PubInv/Ox/mech/enclosure/FreeCADAssy/ControllerSupportRT/README.md

# Files Description
These files are for a bracket to support the Controller V1 PCB to the front panel



With Controler V1 PWA (Printed Wiring Assembly).
