PubInv/Ox/docs/img/Public Invention CC0 and CC-BY-SA License Statement.pdf

Public Invention's Ox Project is an open-source hardware design for an oxygen concentrator for use by field hospitals around the world. This design concept aims to develop an oxygen concentrator that can be manufactured locally while also overcoming challenges posed by human resources, hospital location (geographically), infrastructure and logistics; in addition, this project attempts minimum documentation of their design standards necessary for local approval whilst tackling regulatory requirements for medical devices. Copyright (C) 2021 Robert Read, Ben Coombs, and Darío Hereñú.

Within this folder, all documentation files included fall under the CC0 common domain license published by the creative commons here: https://creativecommons.org/publicdomain/zero/1.0/

Likewise, all graphic art files included fall under the Attribution-ShareAlike license 4.0 International as published by the creative commons here: https://creativecommons.org/licenses/by-sa/4.0/

This program is distributed in the hope that it will be useful, but WITHOUT ANY WARRANTY; without even the implied warranty of MERCHANTABILITY or FITNESS FOR A PARTICULAR PURPOSE.
