PubInv/Ox/elec/Control Board/Control v1/resources/B24B/C545730_B24B-XADSS-N-A(LF)(SN).pdf

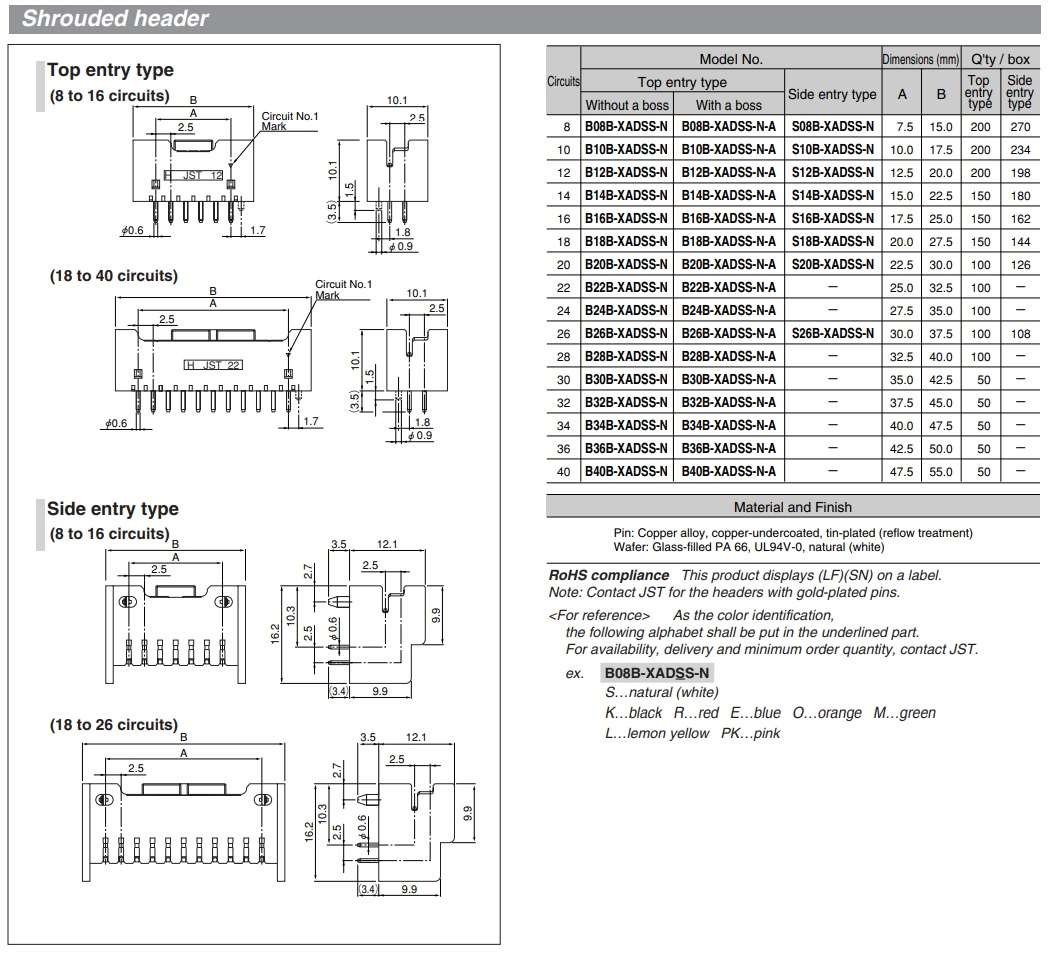
[picture p14: figure]
