PubInv/Ox/docs/img/ventmonadaptor.jpg

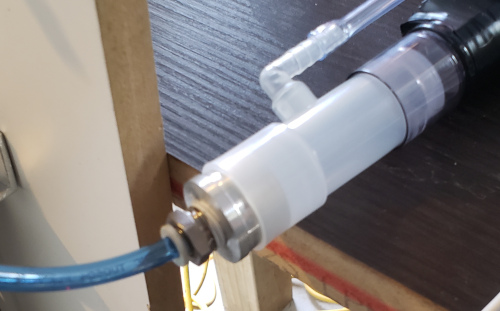
docs/img/ventmonadaptor.jpg
