PubInv/Ox/docs/OEDCS_June_2023_Version_0.1/Photos/AndersonConnectorLowVoltageHighAmperage.JPG

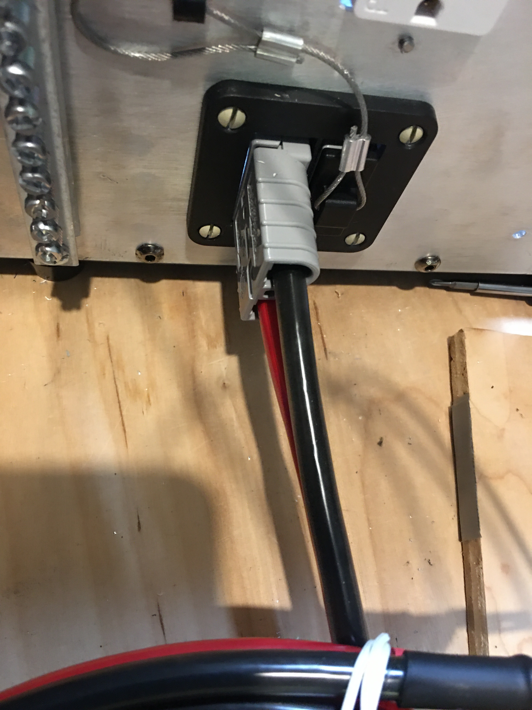
docs/OEDCS_June_2023_Version_0.1/Photos/AndersonConnectorLowVoltageHighAmperage.JPG
