PubInv/Ox/docs/OEDCS_June_2023_Version_0.1/Photos/Draft of Connected System.JPG

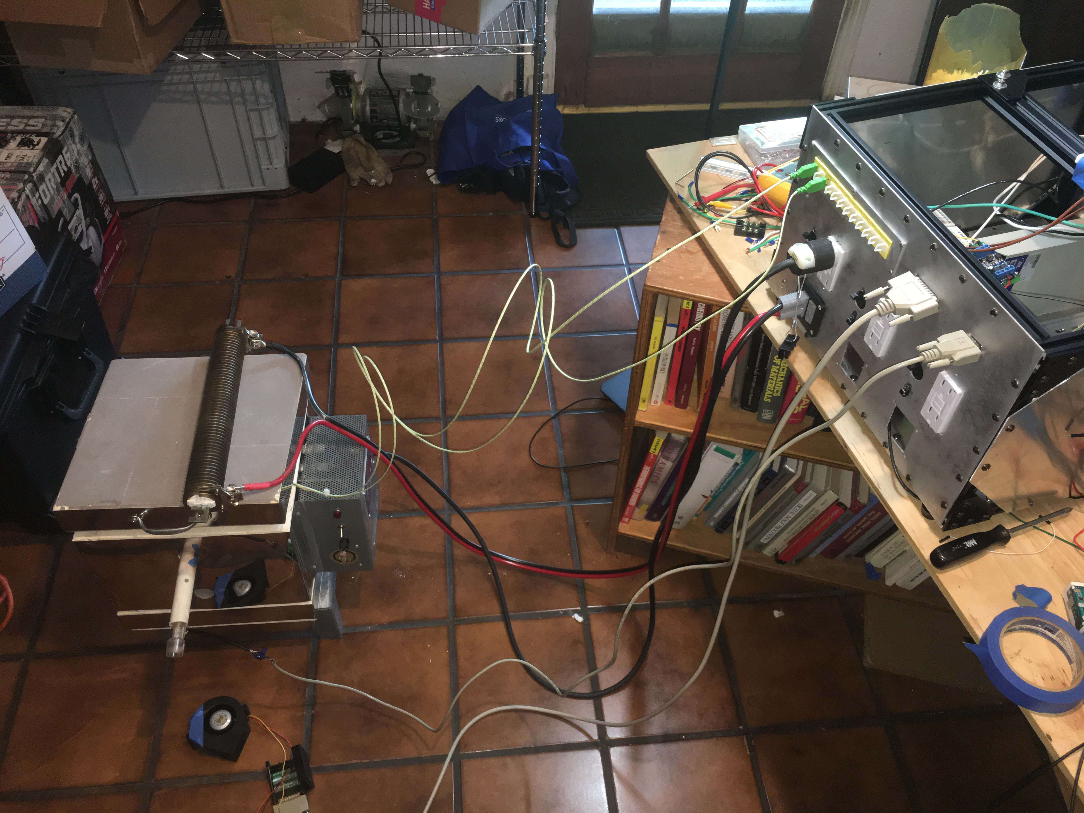
docs/OEDCS_June_2023_Version_0.1/Photos/Draft of Connected System.JPG
