PubInv/Ox/docs/OEDCS_June_2023_Version_0.1/Photos/IMG_4088.JPG

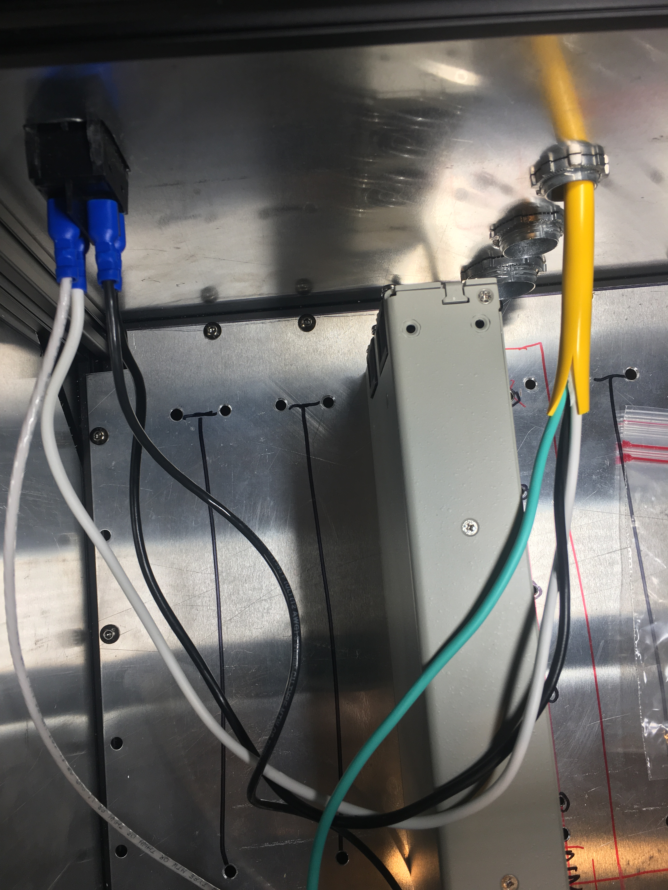
docs/OEDCS_June_2023_Version_0.1/Photos/IMG_4088.JPG
