PubInv/Ox/docs/OEDCS_June_2023_Version_0.1/Photos/OEDICOSBackOfInterFacePanel.JPG

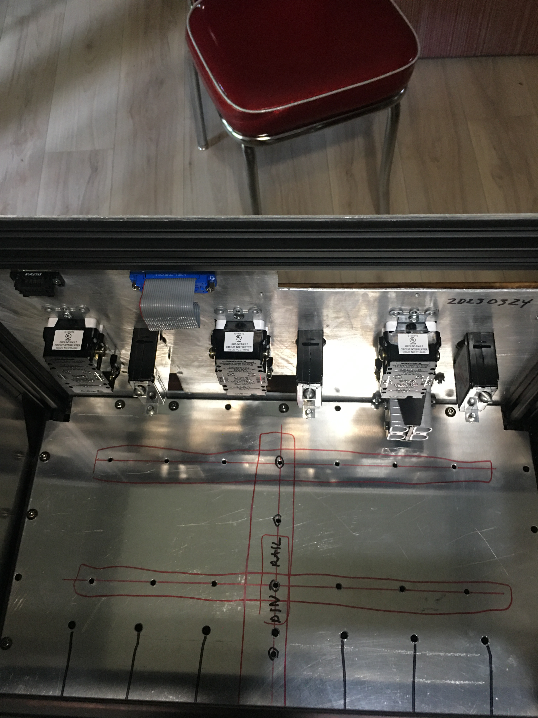
docs/OEDCS_June_2023_Version_0.1/Photos/OEDICOSBackOfInterFacePanel.JPG
