PubInv/Ox/docs/OEDCS_June_2023_Version_0.1/Photos/ThermocouplePanel(1).JPG

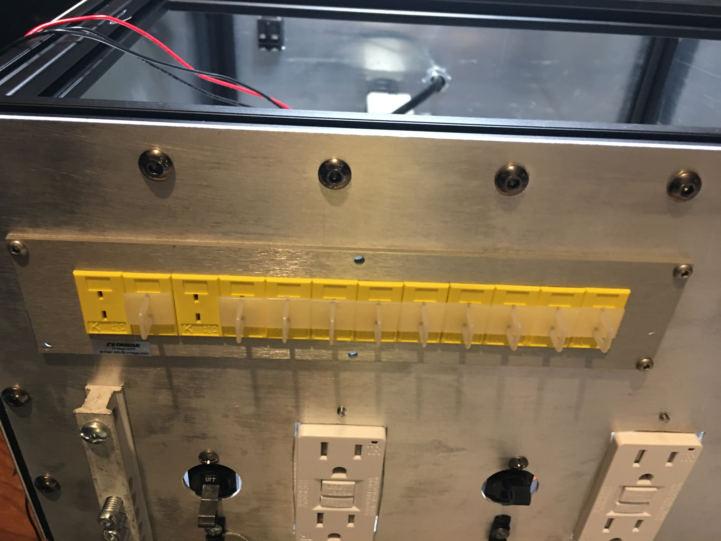
docs/OEDCS_June_2023_Version_0.1/Photos/ThermocouplePanel(1).JPG
