PubInv/Ox/docs/references/datasheets/elec/adafruit_feather_esp32.jpg

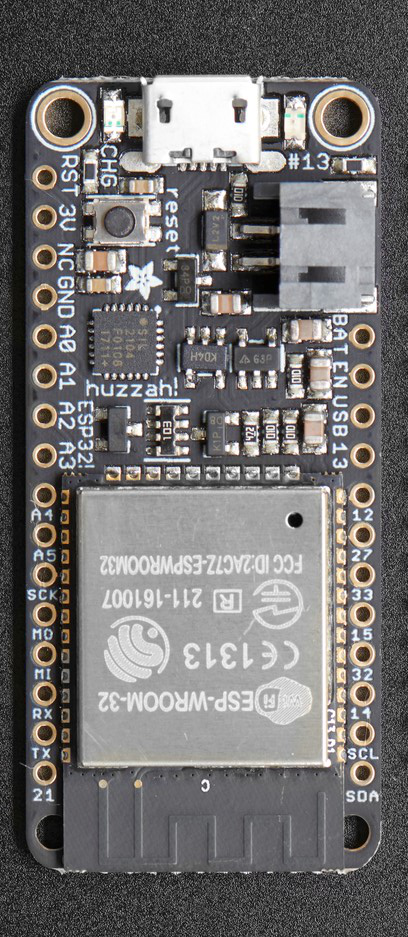
docs/references/datasheets/elec/adafruit_feather_esp32.jpg
