PubInv/Ox/docs/references/datasheets/elec/adafruit_feather_esp32_back.jpg

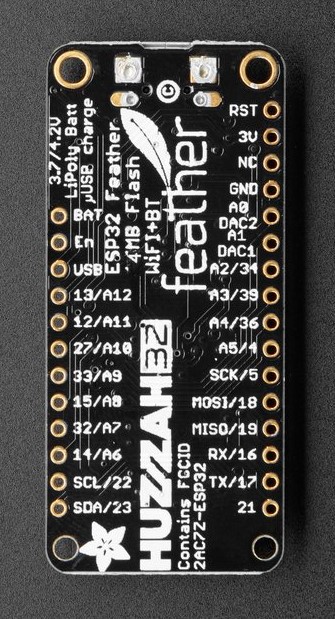
docs/references/datasheets/elec/adafruit_feather_esp32_back.jpg
