PubInv/Ox/elec/Control Board/Control v1/resources/Adafruit_MAX31850.png

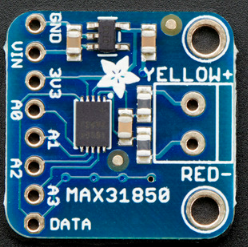
elec/Control Board/Control v1/resources/Adafruit_MAX31850.png
