PubInv/Ox/elec/Control Board/Control v1/resources/Adafruit_MAX31855.png

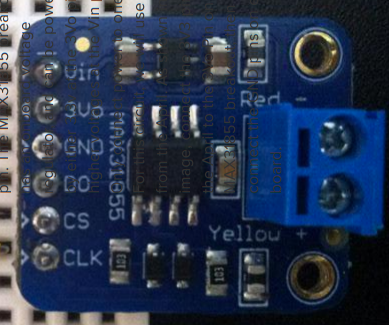
elec/Control Board/Control v1/resources/Adafruit_MAX31855.png
