PubInv/Ox/elec/Control Board/Control v1/resources/Adafruit_MAX31856.png

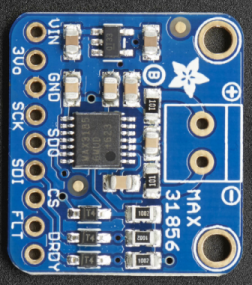
elec/Control Board/Control v1/resources/Adafruit_MAX31856.png
