PubInv/Ox/elec/Control Board/Control v1/resources/Adafruit_MCP9600.png

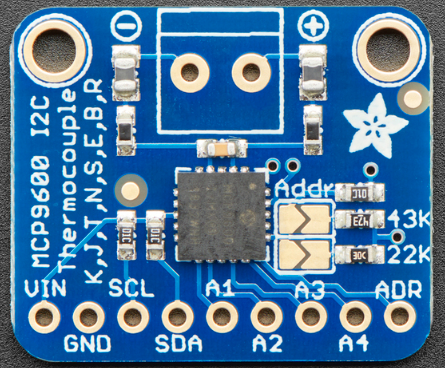
elec/Control Board/Control v1/resources/Adafruit_MCP9600.png
