PubInv/Ox/mech/enclosure/Serial_number2/Boards20230828/Due_Controller_Ethernet.jpg

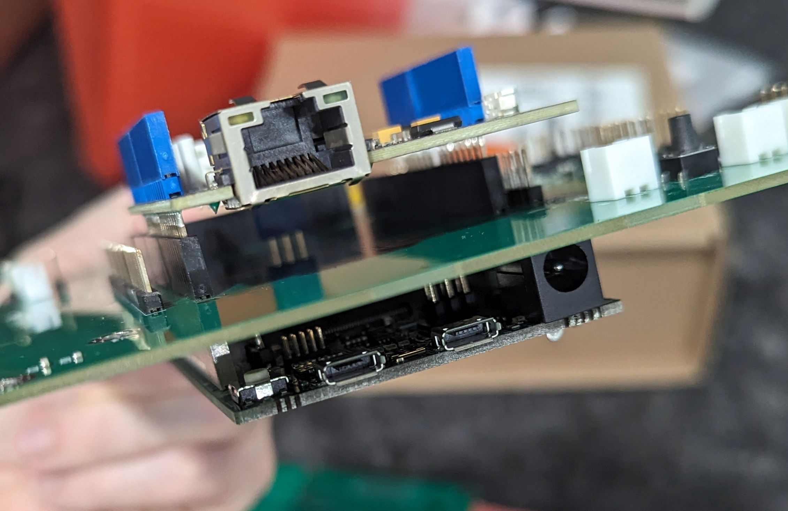
mech/enclosure/Serial_number2/Boards20230828/Due_Controller_Ethernet.jpg
