PubInv/Ox/mech/enclosure/Serial_number2/Boards20230828/ThreePCB_TwoAssy.jpg

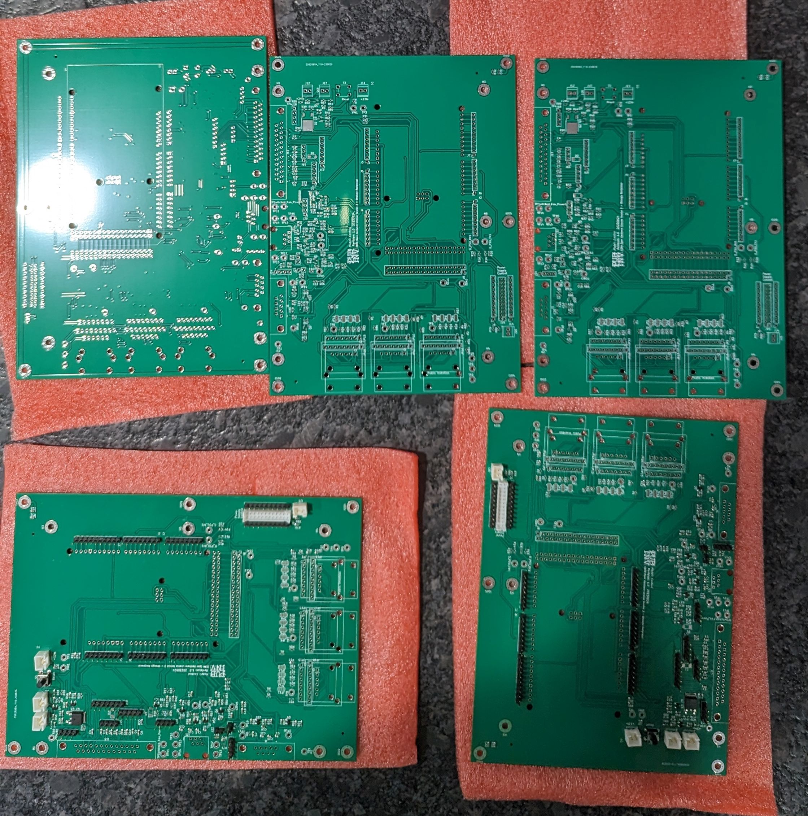
mech/enclosure/Serial_number2/Boards20230828/ThreePCB_TwoAssy.jpg
