PubInv/Ox/mech/frontpanel/Parts/Mech/mpj-j-f-thermocouple/MSS_Series.pdf

# Snap Strips

# For Mounting Miniature

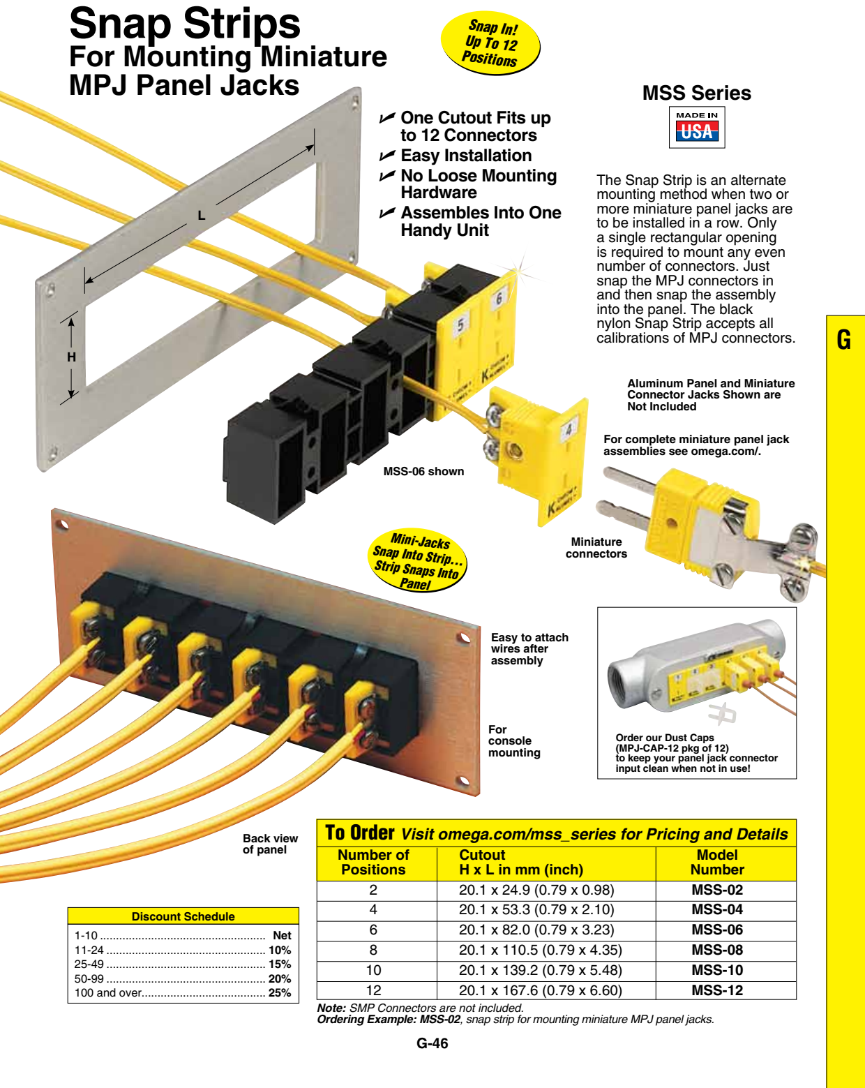
[picture p43: page 1]

# MPJ Panel Jacks

### U One Cutout Fits up to 12 Connectors U Easy Installation U No Loose Mounting Hardware U Assembles Into One Handy Unit

To Order Visit omega.com/mss_series for Pricing and Details
Number of | Cutout | Model
Positions | H x L in mm (inch) | Number
2 | 20.1 x 24.9 (0.79 x 0.98) | MSS-02
4 | 20.1 x 53.3 (0.79 x 2.10) | MSS-04
6 | 20.1 x 82.0 (0.79 x 3.23) | MSS-06
8 | 20.1 x 110.5 (0.79 x 4.35) | MSS-08
10 | 20.1 x 139.2 (0.79 x 5.48) | MSS-10
12 | 20.1 x 167.6 (0.79 x 6.60) | MSS-12

For
console
mounting

Aluminum Panel and Miniature Connector Jacks Shown are
Not Included

Easy to attach
wires after
assembly

Back view
of panel

The Snap Strip is an alternate mounting method when two or more miniature panel jacks are to be installed in a row. Only a single rectangular opening is required to mount any even number of connectors. Just snap the MPJ connectors in and then snap the assembly into the panel. The black
nylon Snap Strip accepts all calibrations of MPJ connectors.

L

H

Miniature
connectors

MSS-06 shown

For complete miniature panel jack assemblies see omega.com/.

Order our Dust Caps
(MPJ-CAP-12 pkg of 12)
to keep your panel jack connector input clean when not in use!

Note: SMP Connectors are not included.
Ordering Example: MSS-02, snap strip for mounting miniature MPJ panel jacks.
G-46

G

Mini-Jacks
Snap Into Strip...
Strip Snaps Into
Panel

Snap In!
Up To 12
Positions
1-10 | Net
11-24 | 10%
25-49 | 15%
50-99 | 20%
100 and over | 25%

Discount Schedule

## MSS Series
