PubInv/Ox/mech/frontpanel/Parts/Outlet/README.txt

This file
Found at: https://grabcad.com/library/gfci-wall-outlet-1
