PubInv/Ox/mech/frontpanel/Parts/Anderson_SB50_PanelDuplex.png

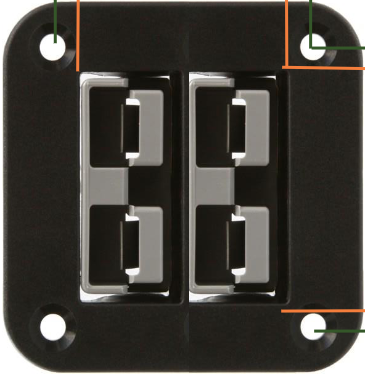
mech/frontpanel/Parts/Anderson_SB50_PanelDuplex.png
