PubInv/Ox/mech/frontpanel/Parts/DB9Female.png

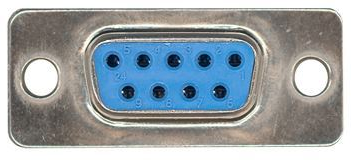
mech/frontpanel/Parts/DB9Female.png
