PubInv/Ox/mech/frontpanel/Parts/DecoratorRecepticalCover.png

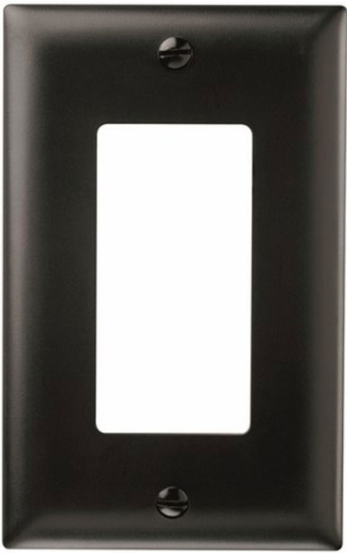
mech/frontpanel/Parts/DecoratorRecepticalCover.png
