PubInv/Ox/mech/frontpanel/Parts/Mech/DSUB9.JPG

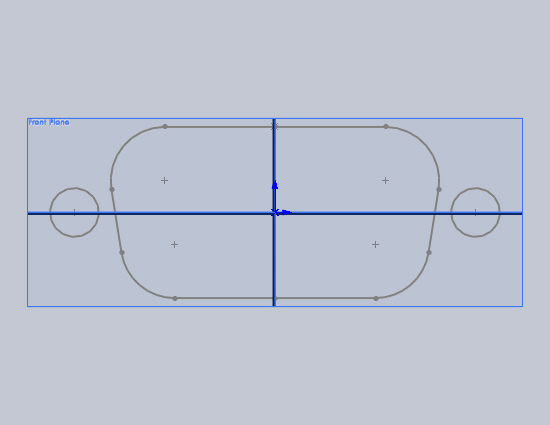
mech/frontpanel/Parts/Mech/DSUB9.JPG
