PubInv/Ox/mech/frontpanel/Parts/Mech/IEC_Receptical/IES_Cord_220_20A.jpg

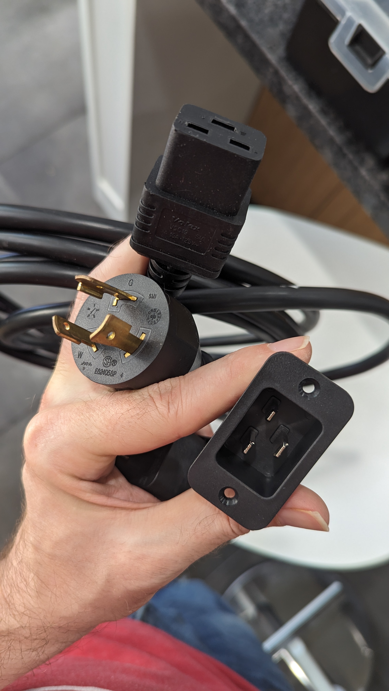
mech/frontpanel/Parts/Mech/IEC_Receptical/IES_Cord_220_20A.jpg
