PubInv/Ox/mech/frontpanel/Parts/Mech/mpj-j-f-thermocouple/example_MJP-12-K.jpg

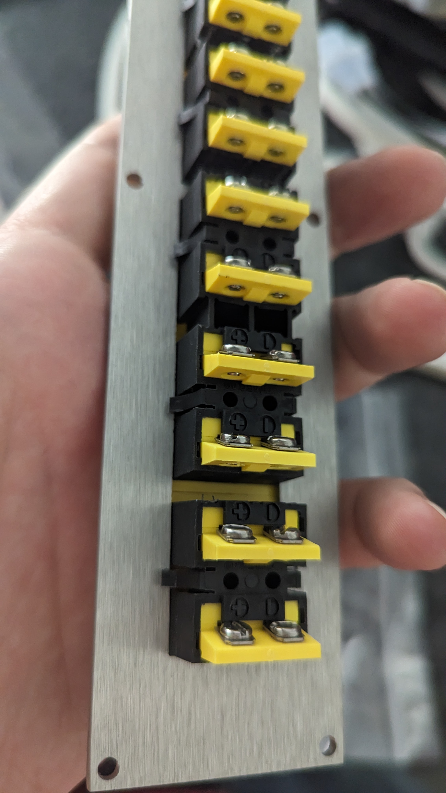
mech/frontpanel/Parts/Mech/mpj-j-f-thermocouple/example_MJP-12-K.jpg
