PubInv/Ox/mech/frontpanel/Parts/Mech/mpj-j-f-thermocouple/example_MPJ-K-F.jpg

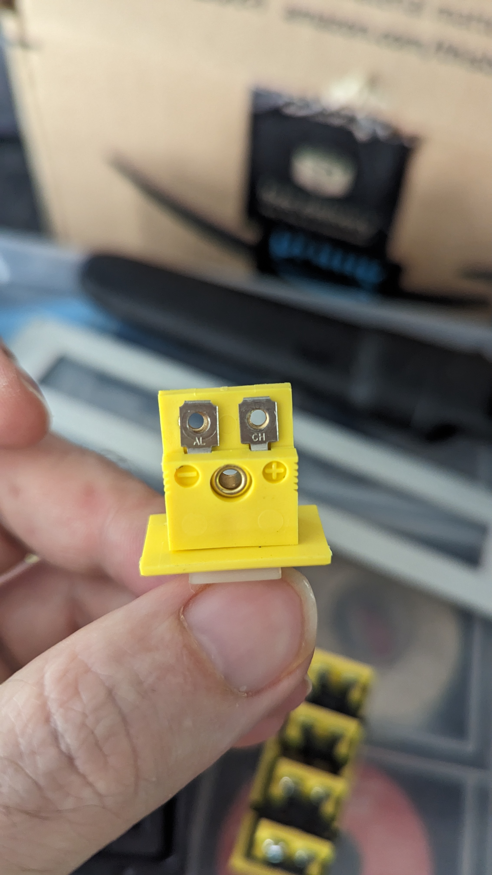
mech/frontpanel/Parts/Mech/mpj-j-f-thermocouple/example_MPJ-K-F.jpg
