PubInv/Ox/mech/frontpanel/Parts/Outlet/GFCI - Leviton Outlet.JPG

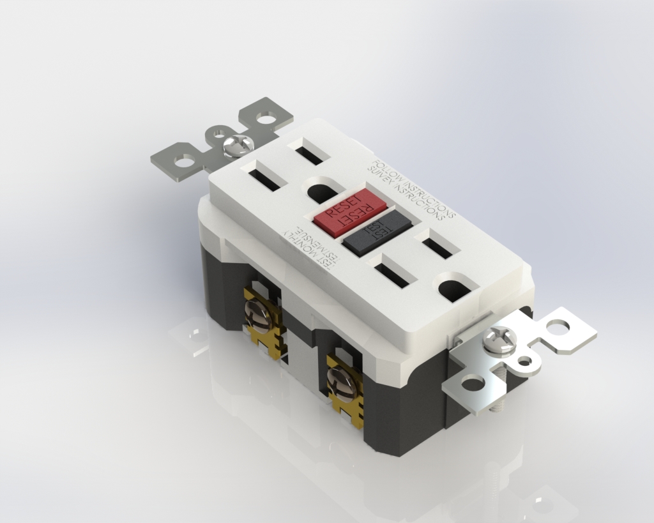
mech/frontpanel/Parts/Outlet/GFCI - Leviton Outlet.JPG
