PubInv/Ox/elec/fan_I2C/fan_I2C/parts/3D/Amphenol_54601_RT_ANGLE.step

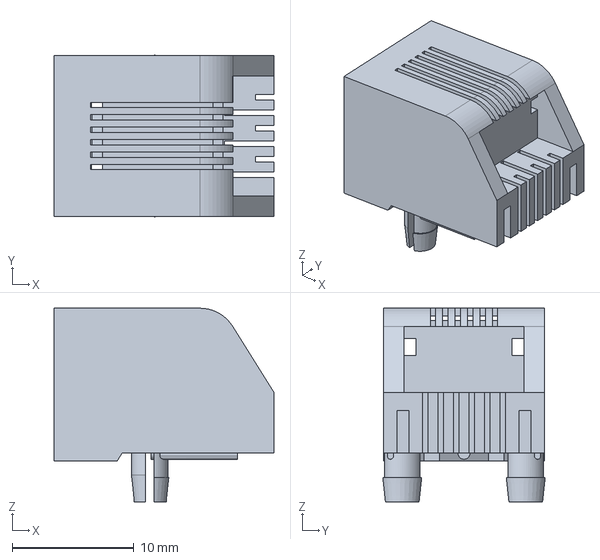
[picture p73: CAD file, 2023-09-07]
elec/fan_I2C/fan_I2C/parts/3D/Amphenol_54601_RT_ANGLE.step
18.1 x 13.4 x 15.9 mm
