PubInv/Ox/mech/enclosure/3D models/enclosure.stl

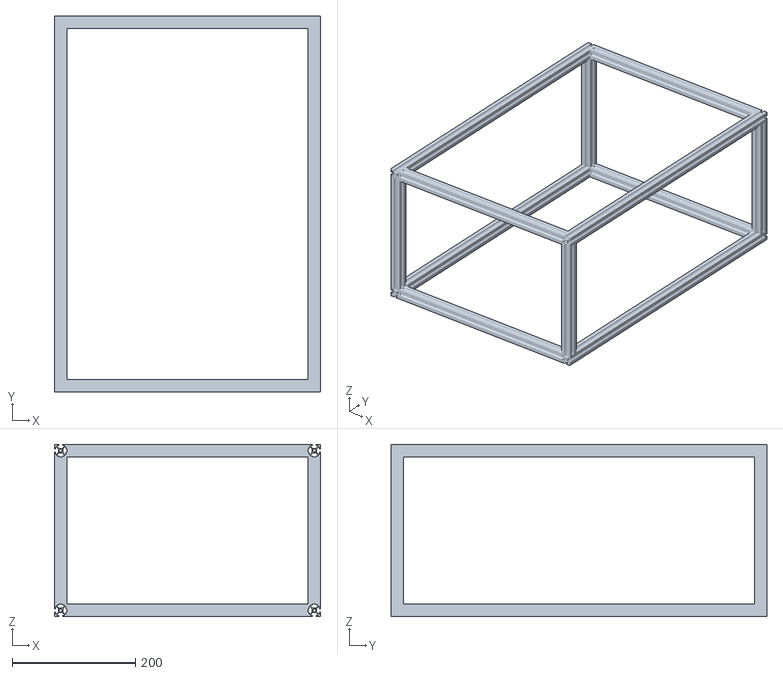
[picture p74: CAD file, 2023-09-07]
mech/enclosure/3D models/enclosure.stl
431.8 x 609.6 x 279.4
