PubInv/Ox/mech/enclosure/FreeCADAssy/ControllerSupportRT/ControllerSupportRT-PartBodySupportRT.step

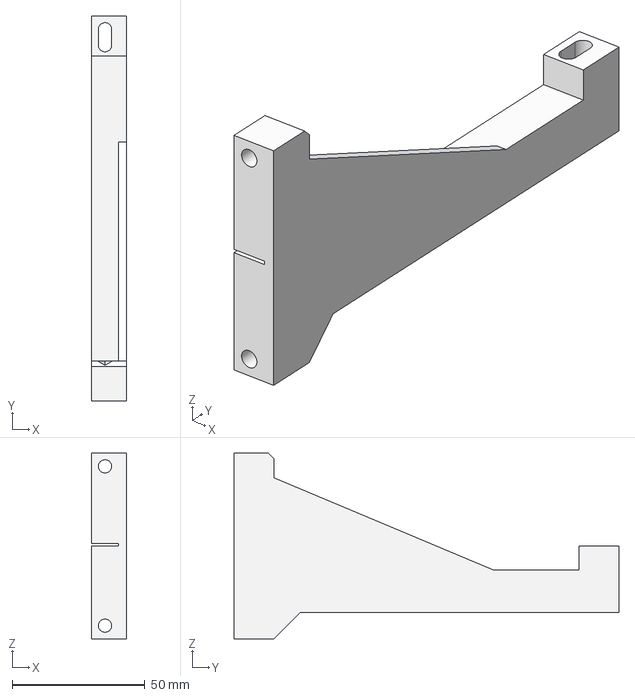
[picture p75: CAD file, 2023-09-07]
mech/enclosure/FreeCADAssy/ControllerSupportRT/ControllerSupportRT-PartBodySupportRT.step
13.0 x 145.0 x 70.0 mm
