PubInv/Ox/mech/frontpanel/Parts/Mech/Gusseted 2020 corner bracket v2.step

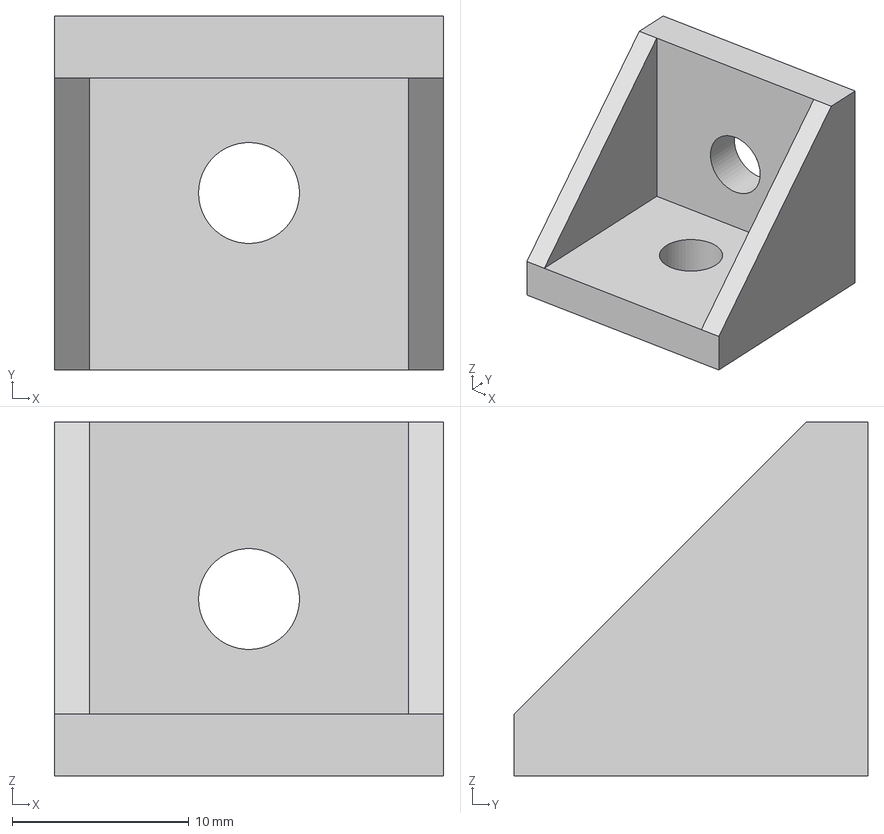
[picture p76: CAD file, 2023-09-07]
mech/frontpanel/Parts/Mech/Gusseted 2020 corner bracket v2.step
22.0 x 20.0 x 20.0 mm
