PubInv/Ox/mech/frontpanel/Parts/Mech/mpj-j-f-thermocouple/JackPanel_MJP-Part_JP6BodyJP6.step

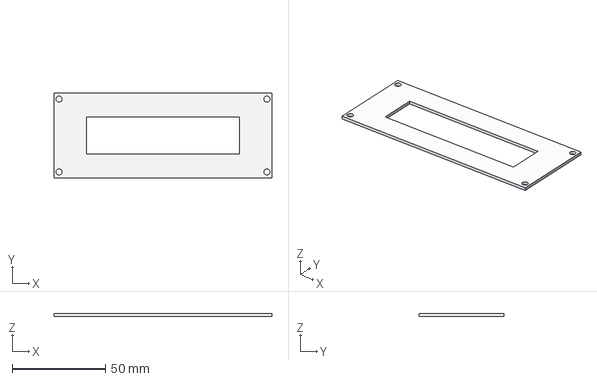
[picture p77: CAD file, 2023-09-07]
mech/frontpanel/Parts/Mech/mpj-j-f-thermocouple/JackPanel_MJP-Part_JP6BodyJP6.step
117.0 x 45.6 x 1.59 mm
