PubInv/Ox/mech/frontpanel/Parts/PowerWerx/PanelPlate_SB-PartBodySB1.step

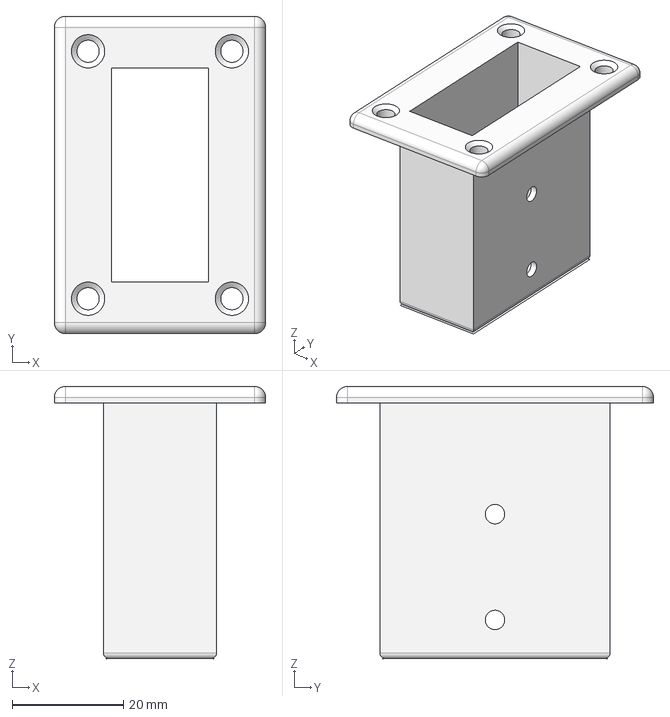
[picture p78: CAD file, 2023-09-07]
mech/frontpanel/Parts/PowerWerx/PanelPlate_SB-PartBodySB1.step
38.1 x 57.1 x 49.0 mm
