PubInv/Ox/mech/frontpanel/RearPanel3.step

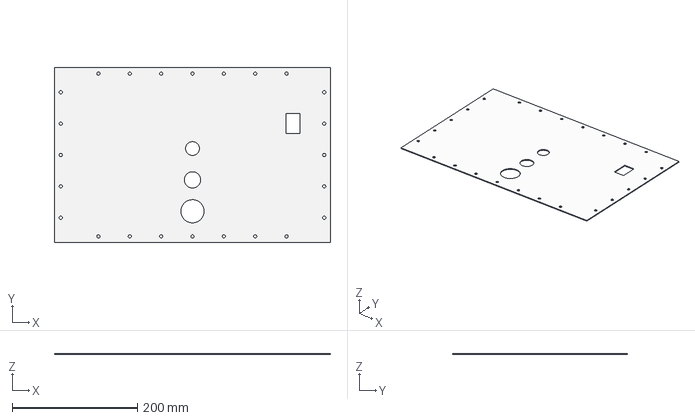
[picture p79: CAD file, 2023-09-07]
mech/frontpanel/RearPanel3.step
440.0 x 279.4 x 1.57 mm
