PubInv/Ox/mech/enclosure/FreeCADAssy/ControllerSupportRT/ControllerSupportRT-CloneBodySupportLR.step

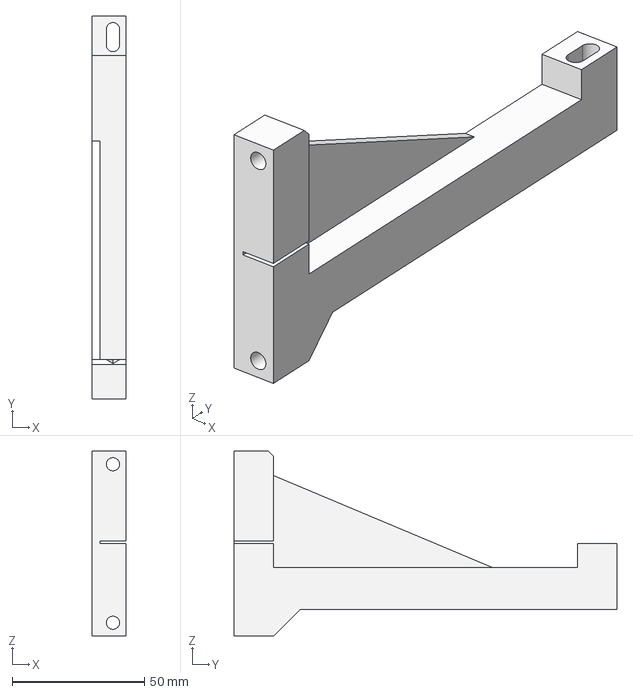
[picture p80: CAD file, 2023-09-07]
mech/enclosure/FreeCADAssy/ControllerSupportRT/ControllerSupportRT-CloneBodySupportLR.step
13.0 x 145.0 x 70.0 mm
