PubInv/Ox/mech/frontpanel/frontpanel_Rev1_3.dxf

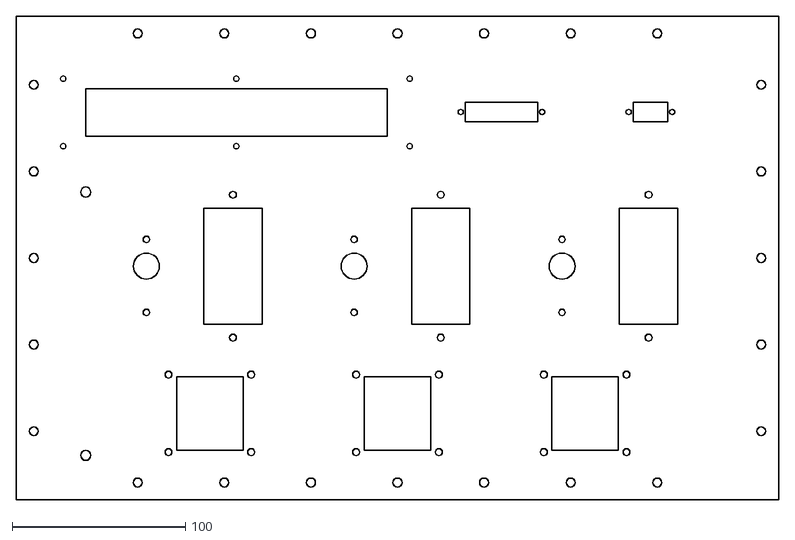
[picture p81: CAD file, 2023-09-07]
mech/frontpanel/frontpanel_Rev1_3.dxf
440.0 x 279.4
