PubInv/Ox/mech/frontpanel/Parts/Mech/alu extrusion profile 2020.step

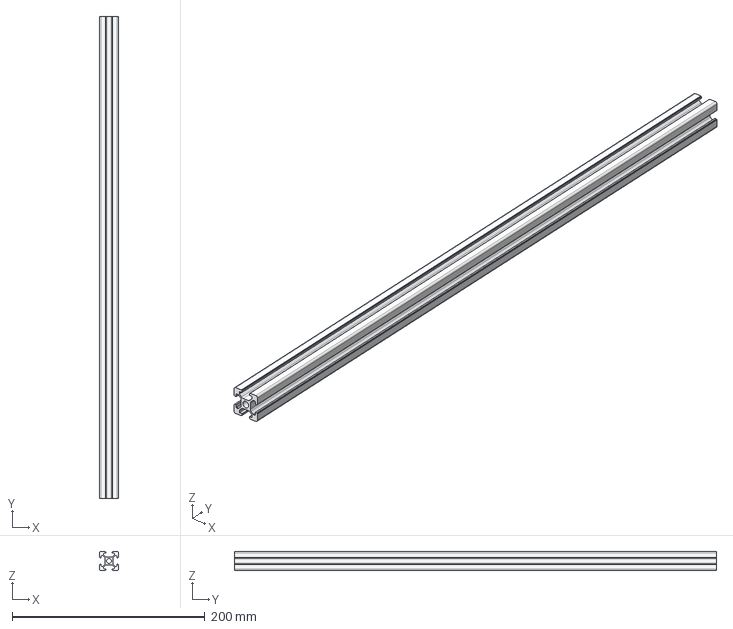
[picture p82: CAD file, 2023-09-07]
mech/frontpanel/Parts/Mech/alu extrusion profile 2020.step
20.0 x 500.0 x 20.0 mm
