PubInv/Ox/mech/frontpanel/Parts/Mech/mpj-j-f-thermocouple/MPJ-J-F Thermocouple Connector, OMEGA.STEP

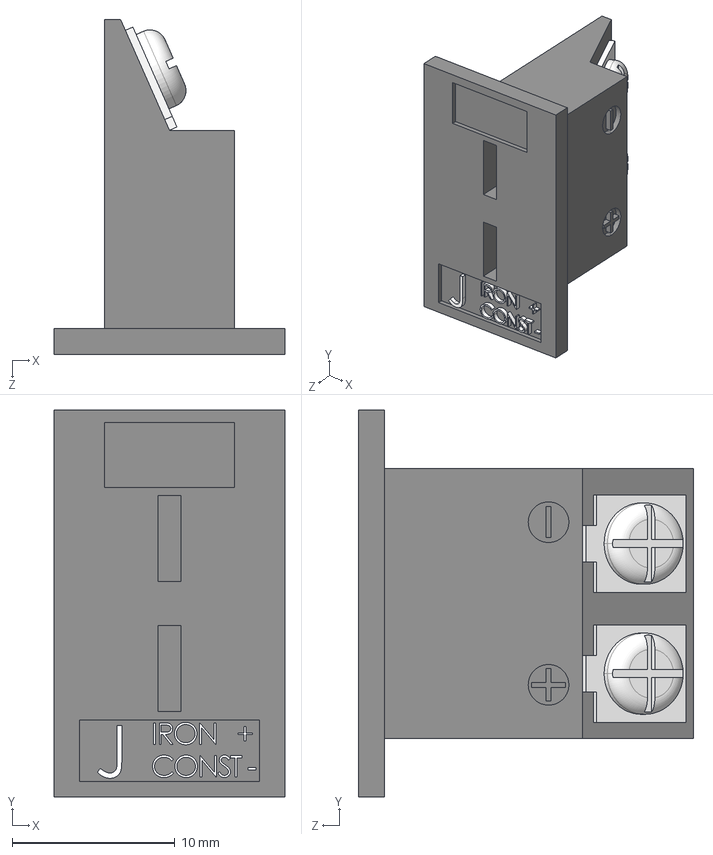
[picture p83: CAD file, 2023-09-07]
mech/frontpanel/Parts/Mech/mpj-j-f-thermocouple/MPJ-J-F Thermocouple Connector, OMEGA.STEP
14.2 x 23.8 x 20.6 mm
