PubInv/Ox/mech/frontpanel/frontpanel-PartFrontPanel2frontpanel2.step

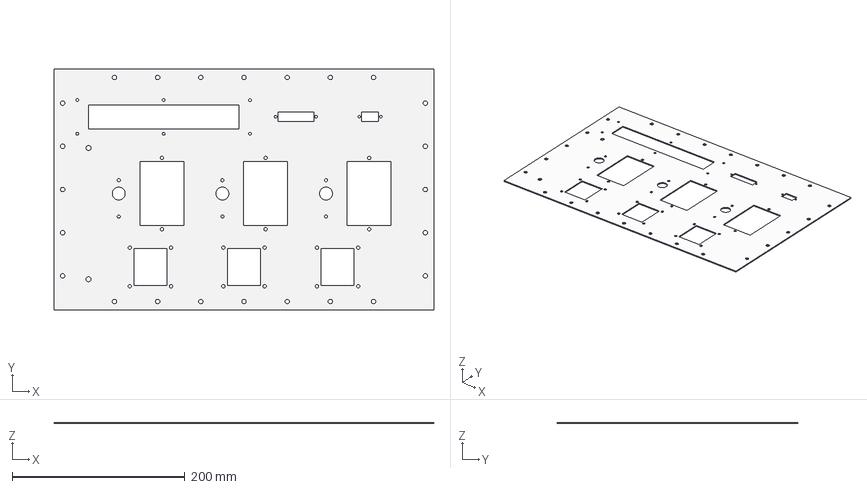
[picture p84: CAD file, 2023-09-07]
mech/frontpanel/frontpanel-PartFrontPanel2frontpanel2.step
440.0 x 279.4 x 1.57 mm
