PubInv/Ox/mech/frontpanel/Parts/Mech/Decora cover v5.step

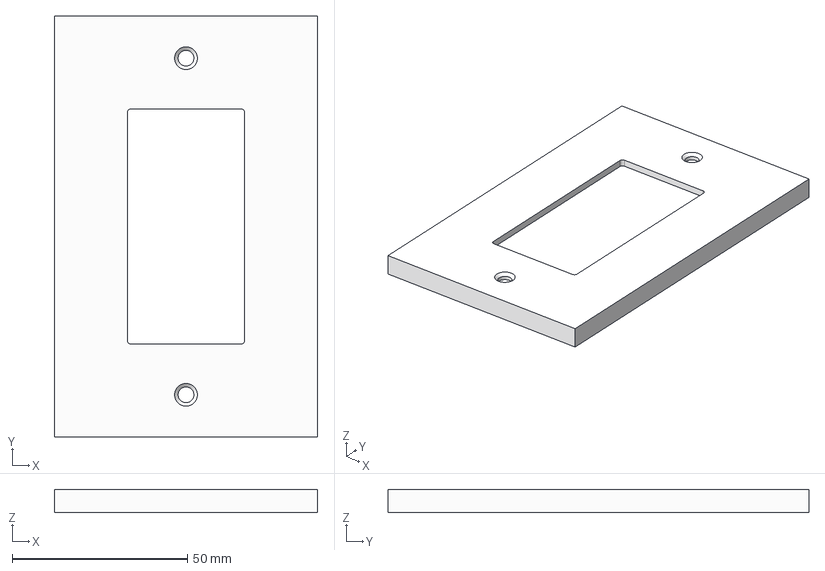
[picture p85: CAD file, 2023-09-07]
mech/frontpanel/Parts/Mech/Decora cover v5.step
75.0 x 120.0 x 6.70 mm
