PubInv/Ox/mech/frontpanel/BottomPlateV1 edit.dxf

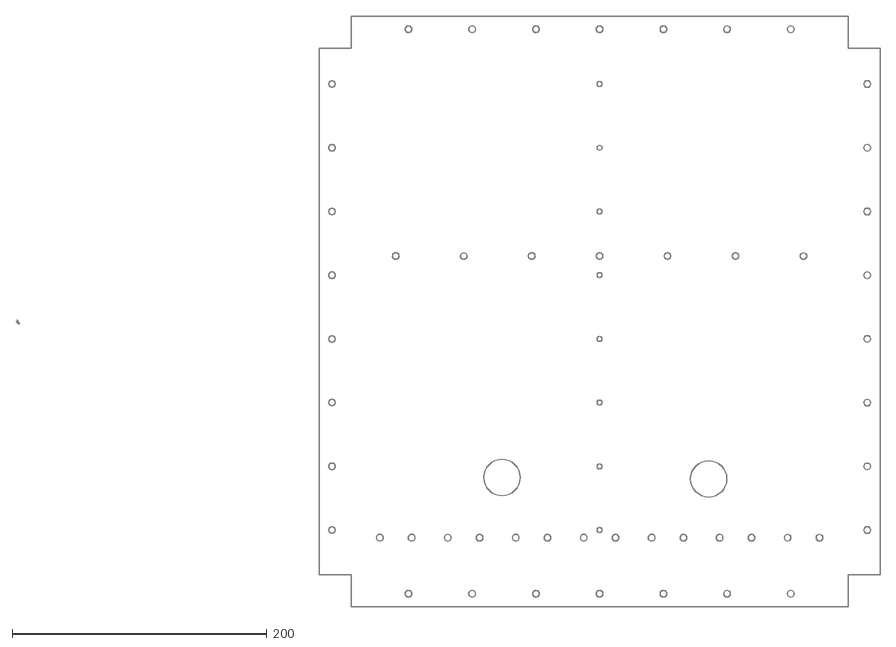
[picture p86: CAD file, 2023-09-07]
mech/frontpanel/BottomPlateV1 edit.dxf
678.0 x 463.0
