PubInv/Ox/mech/frontpanel/rear panel edit 1_3.dxf

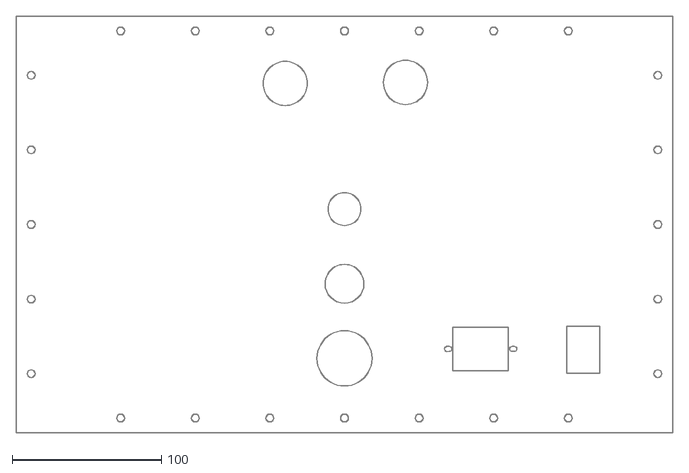
[picture p87: CAD file, 2023-09-07]
mech/frontpanel/rear panel edit 1_3.dxf
440.0 x 279.4
