PubInv/Ox/elec/Control Board/Control v1/Manufacturing Files/README.md

# Discription of these files

The files used to order Control V1 printed wiring assemblies from JLCPCB on about 20230828

* Control v1 bom and placement 28_8_2023 .zip
* Control v1Gerbers 28_8_2023.zip
* bom (3).xls
