PubInv/Ox/mech/enclosure/wiring_enclosure.png

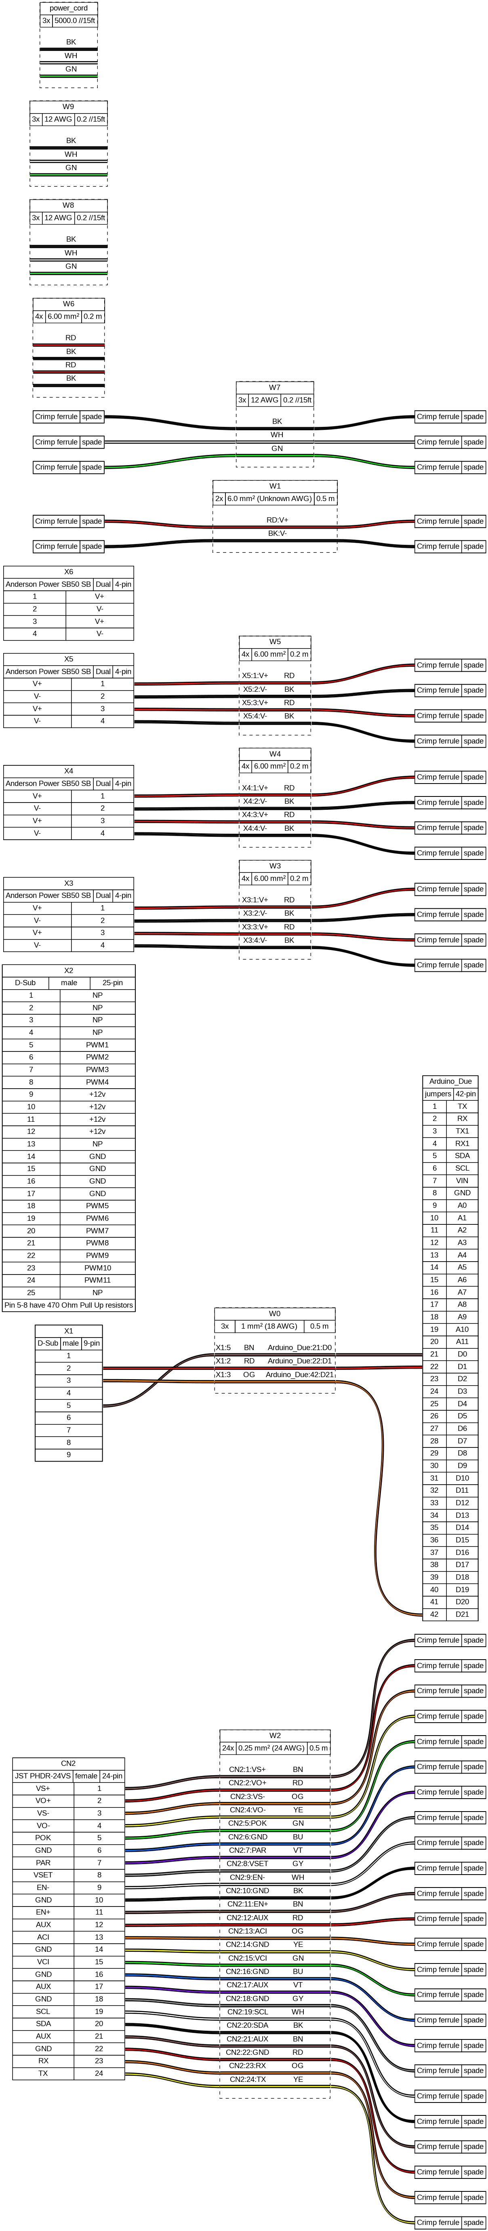
mech/enclosure/wiring_enclosure.png
