PubInv/Ox/mech/frontpanel/Parts/Mech/mpj-j-f-thermocouple/MJP1-06_Drawing.pdf

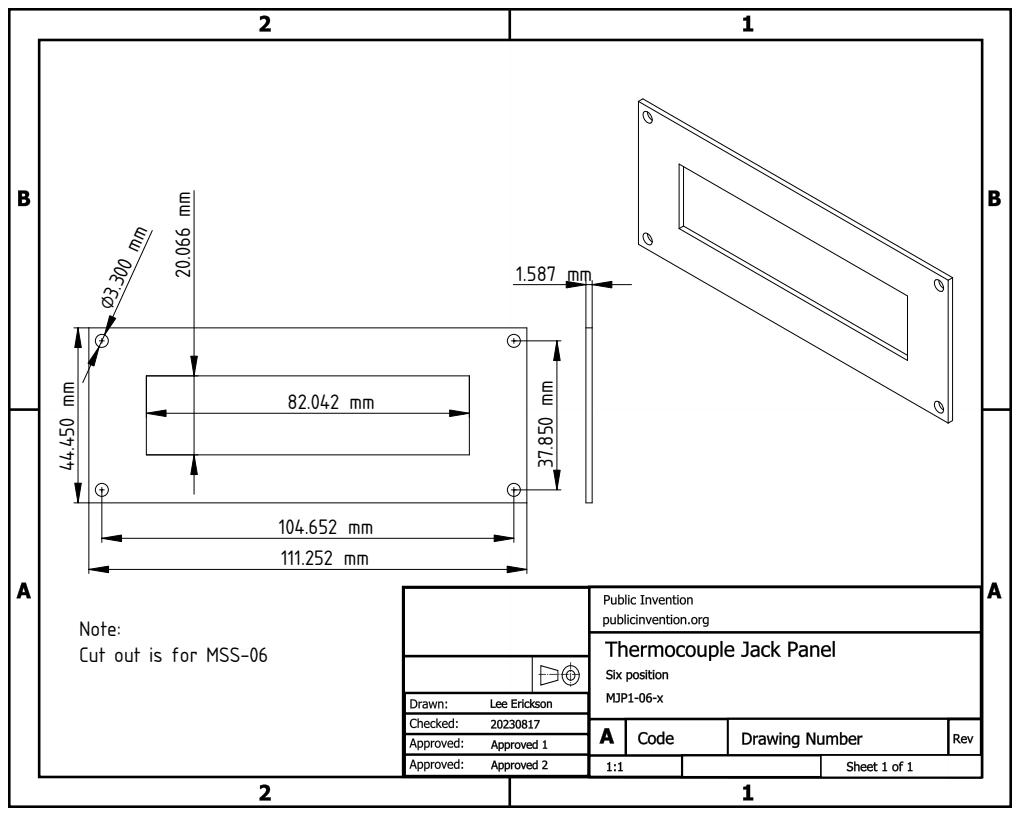
[picture p98: page 1]

Note:
Cut out is for MSS-06
