PubInv/Ox/elec/Control Board/Control v1/resources/PLUGs/C2905415_KH-2.54FH-1X4P-H8.5.pdf

# SPECIFICATIONS

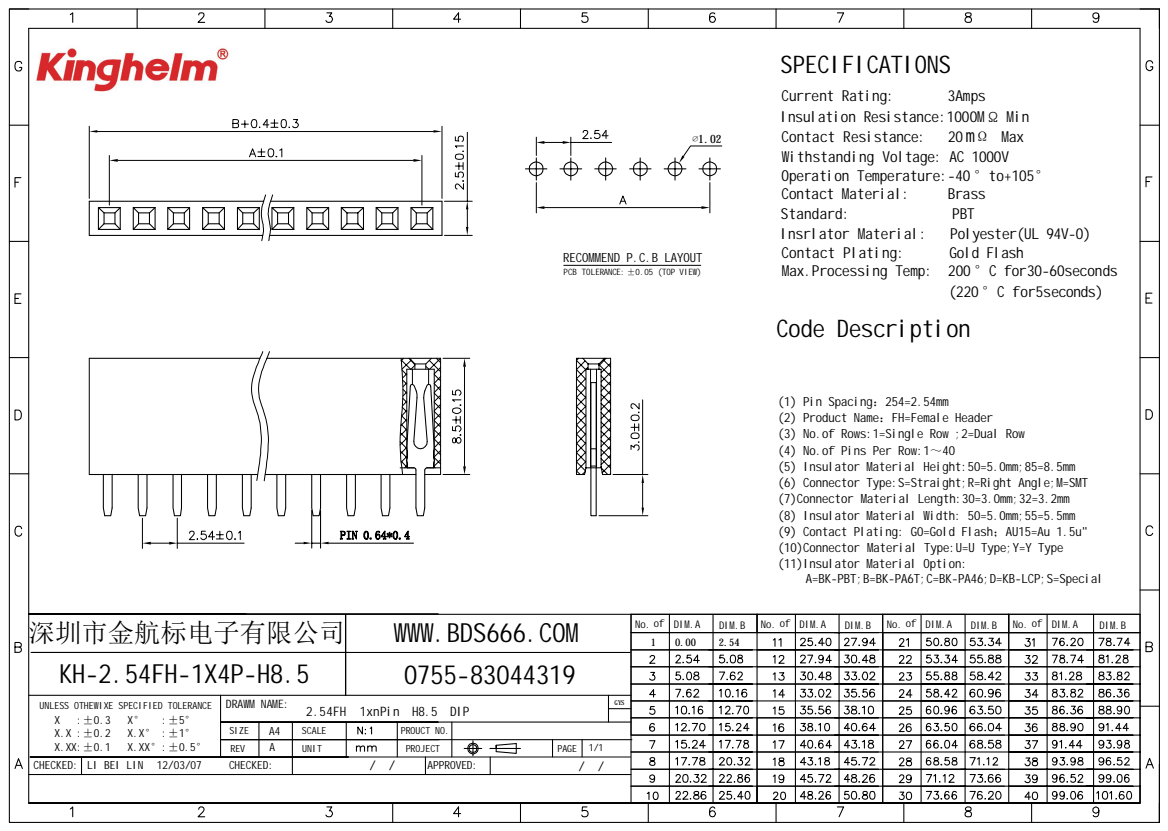
[picture p99: page 1]
2.54FH 1xnPin H8.5 DIP; CHECKED:; LI BEI LIN 12/03/07; REV; SIZE; UNIT; SCALE; UNLESS OTHEWIXE SPECIFIED TOLERANCE; DRAWM NAME:; GYS; PAGE 1/1; APPROVED:; PROUCT NO.; PROJECT; Current Rating:; 3Amps; Contact Resistance:; 20 mΩ Max; Contact Material:; Brass; Standard:; PBT; Insrlator Material:; Polyester(UL 94V-0); Contact Plating:; Gold Flash; (220 °C for5seconds) Code Description; 深圳市金航标电子有限公司; WWW.BDS666.COM

Insulation Resistance:1000M Ω Min
Withstanding Voltage: AC 1000V
Operation Temperature:-40 °to+105°
Max.Processing Temp: 200 °C for30-60seconds

RECOMMEND P.C.B LAYOUT
PCB TOLERANCE: ±0.05 (TOP VIEW)

(1) Pin Spacing：254=2.54mm
(2) Product Name：FH=Female Header
(3) No.of Rows:1=Single Row ;2=Dual Row
(4) No.of Pins Per Row:1～40
(5) Insulator Material Height:50=5.0mm;85=8.5mm
(6) Connector Type:S=Straight;R=Right Angle;M=SMT
(7)Connector Material Length:30=3.0mm;32=3.2mm
(8) Insulator Material Width: 50=5.0mm;55=5.5mm
(9) Contact Plating: G0=Gold Flash；AU15=Au 1.5u"
(10)Connector Material Type:U=U Type;Y=Y Type
(11)Insulator Material Option:
A=BK-PBT;B=BK-PA6T;C=BK-PA46;D=KB-LCP;S=Special

No. of | DIM.A DIM.B | No. of | DIM.A | DIM.B No. of | DIM.A DIM.B | No. of | DIM.A | DIM.B
1 | 0.00 | 2.54
