PubInv/Ox/mech/frontpanel/Parts/PowerWerx/PanelPlate_SB1.pdf

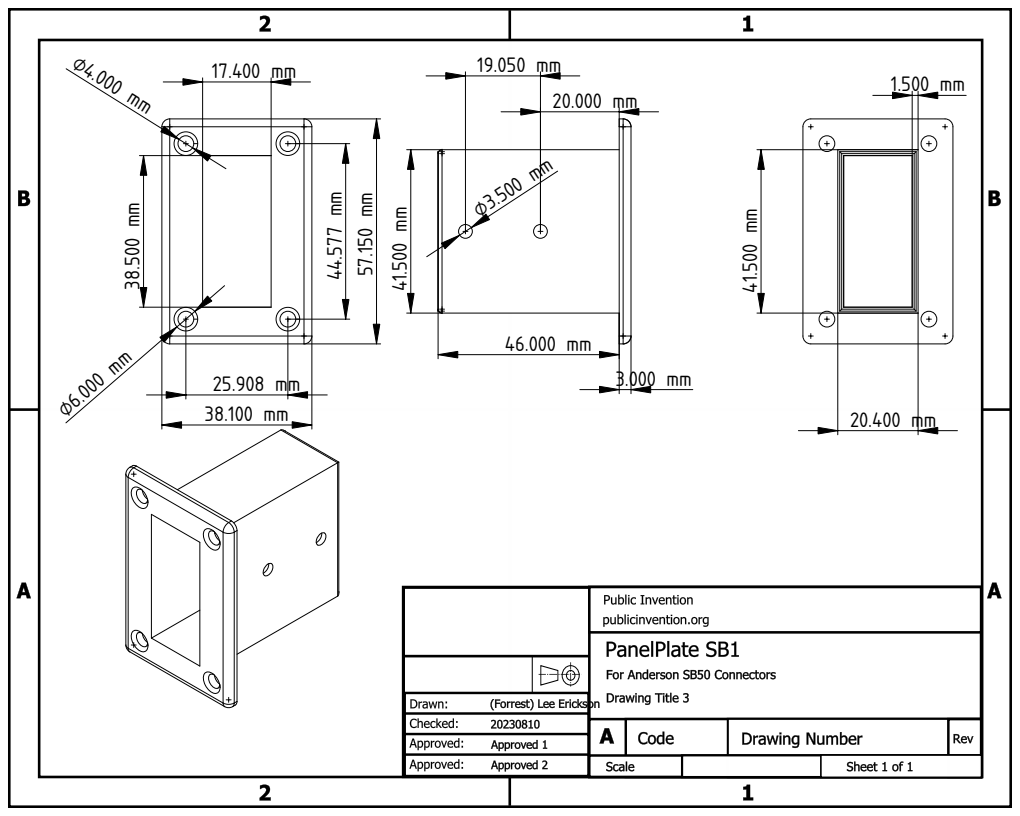
[picture p117: page 1]
