PubInv/Ox/mech/frontpanel/Parts/PowerWerx/PanelPlate_SB2.pdf

m 1.500

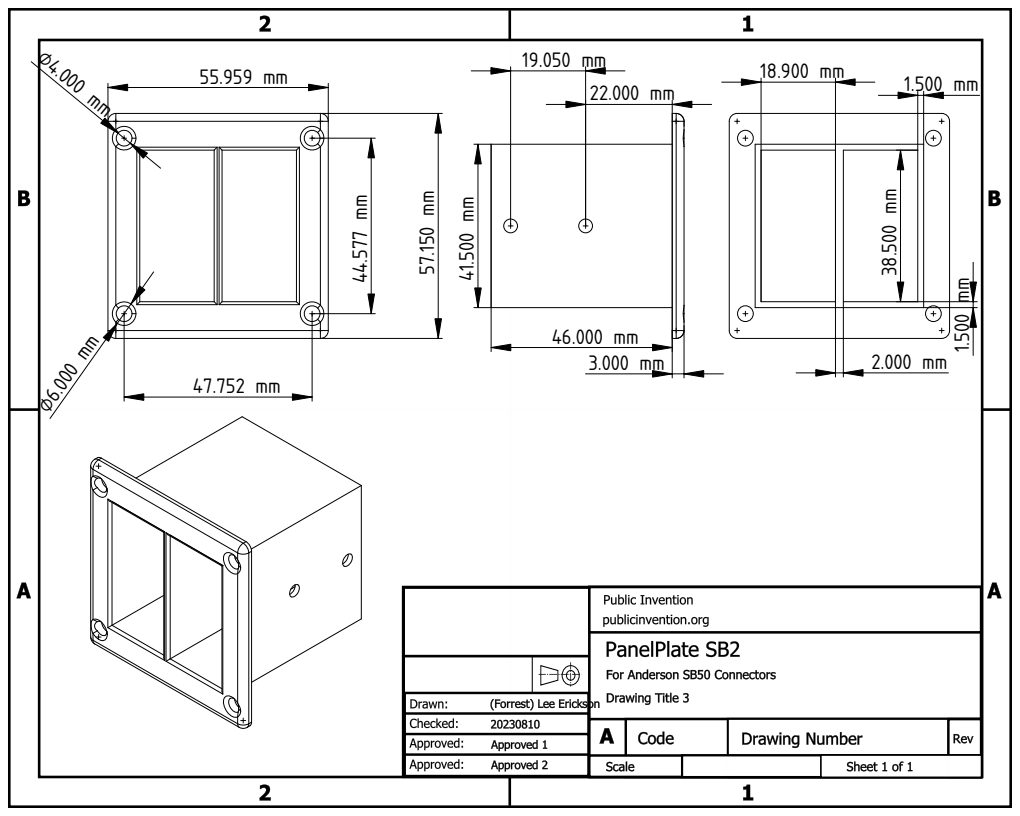
[picture p118: page 1]
