PubInv/Ox/mech/frontpanel/Parts/Mech/mpj-j-f-thermocouple/MSS_B0282761 REV-A.pdf

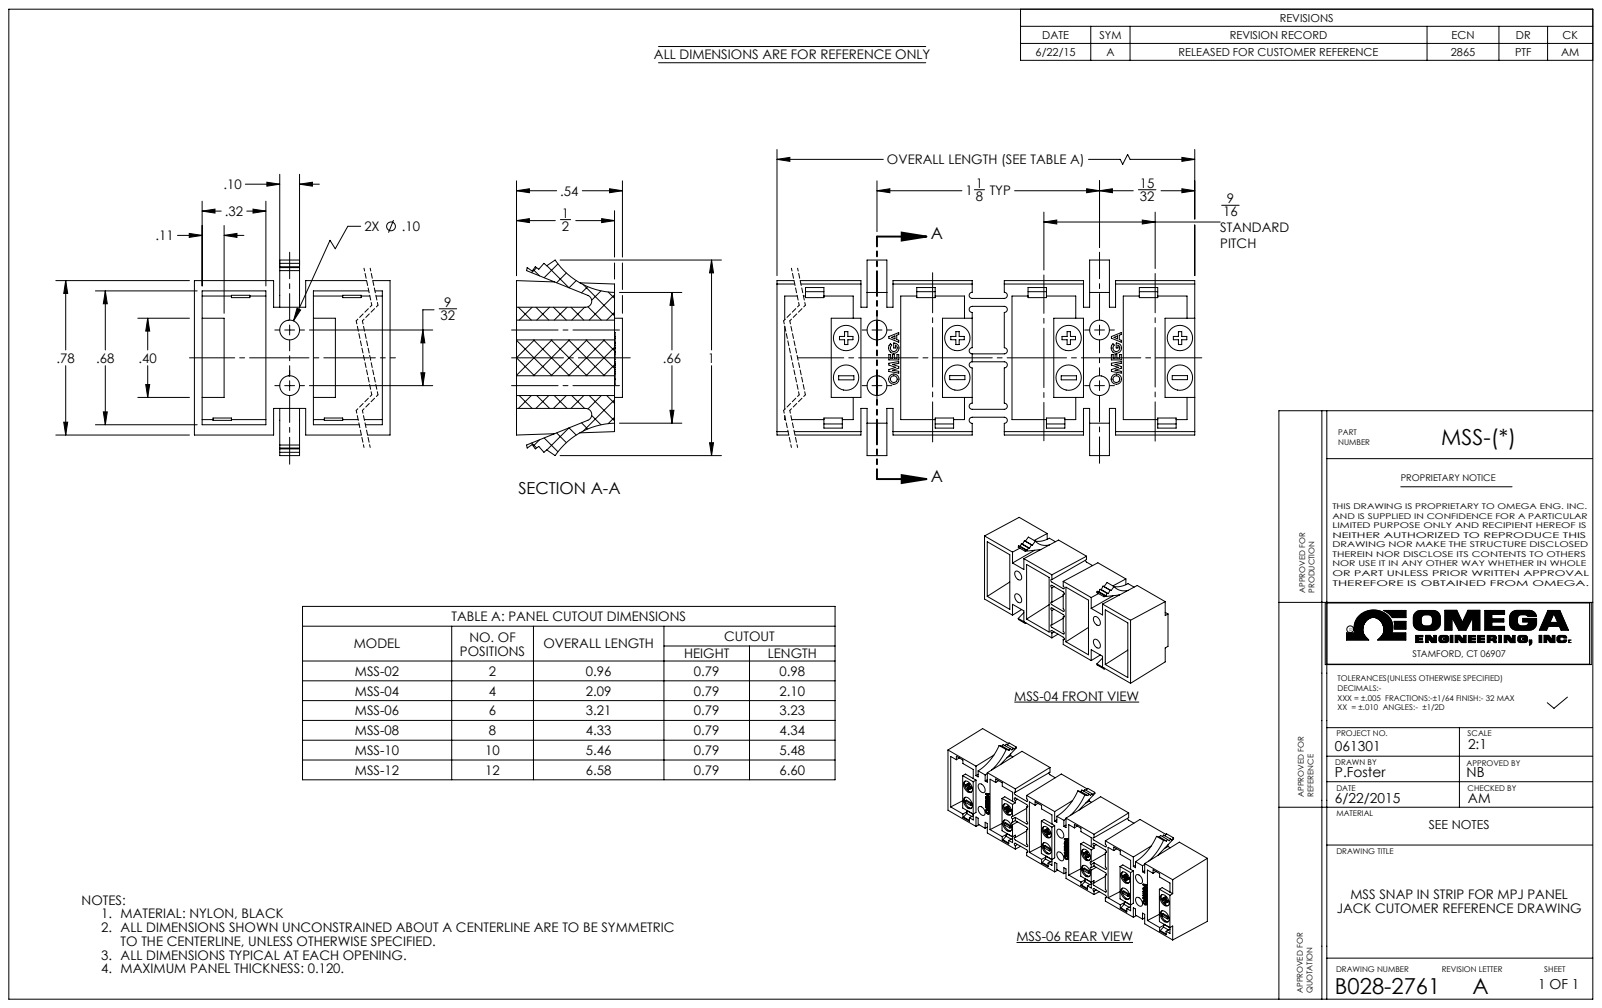
[picture p119: page 1]
DRAWING NUMBER; REVISION LETTER; SHEET; APPROVED FOR; DRAWING TITLE; CHECKED BY; PROPRIETARY NOTICE; 1 1 8 TYP; SECTION A-A; RELEASED FOR CUSTOMER REFERENCE; PTF; SEE NOTES

REVISIONS

DATE | SYM | REVISION RECORD | ECN | DR | CK

ALL DIMENSIONS ARE FOR REFERENCE ONLY

OVERALL LENGTH (SEE TABLE A)

THIS DRAWING IS PROPRIETARY TO OMEGA ENG. INC.
AND IS SUPPLIED IN CONFIDENCE FOR A PARTICULAR
LIMITED PURPOSE ONLY AND RECIPIENT HEREOF IS
NEITHER AUTHORIZED TO REPRODUCE THIS
DRAWING NOR MAKE THE STRUCTURE DISCLOSED
THEREIN NOR DISCLOSE ITS CONTENTS TO OTHERS
NOR USE IT IN ANY OTHER WAY WHETHER IN WHOLE
OR PART UNLESS PRIOR WRITTEN APPROVAL
THEREFORE IS OBTAINED FROM OMEGA.

TABLE A: PANEL CUTOUT DIMENSIONS

MODEL | POSITIONS NO. OF | OVERALL LENGTH | CUTOUT

R STAMFORD, CT 06907 TOLERANCES(UNLESS OTHERWISE SPECIFIED) DECIMALS:-XXX = ±.005 FRACTIONS:-±1/64 FINISH:- 32 MAX XX = ±.010 ANGLES:- ±1/2D

HEIGHT | LENGTH

MSS-02 | 2 | 0.96 | 0.79 | 0.98
MSS-04 | 4 | 2.09 | 0.79 | 2.10
MSS-06 | 6 | 3.21 | 0.79 | 3.23
MSS-08 | 8 | 4.33 | 0.79 | 4.34
MSS-10 | 10 | 5.46 | 0.79 | 5.48
MSS-12 | 12 | 6.58 | 0.79 | 6.60

MSS-04 FRONT VIEW

PROJECT NO. 061301 | SCALE 2:1

DRAWN BY P.Foster | APPROVED BY NB

MSS SNAP IN STRIP FOR MPJ PANEL
JACK CUTOMER REFERENCE DRAWING

NOTES:
1. MATERIAL: NYLON, BLACK
2. ALL DIMENSIONS SHOWN UNCONSTRAINED ABOUT A CENTERLINE ARE TO BE SYMMETRIC
TO THE CENTERLINE, UNLESS OTHERWISE SPECIFIED.
3. ALL DIMENSIONS TYPICAL AT EACH OPENING.
4. MAXIMUM PANEL THICKNESS: 0.120.

MSS-06 REAR VIEW
