PubInv/Ox/mech/frontpanel/Parts/Mech/DB25_DB9/DB25_STEP/ENG_CD_5747846_P.pdf

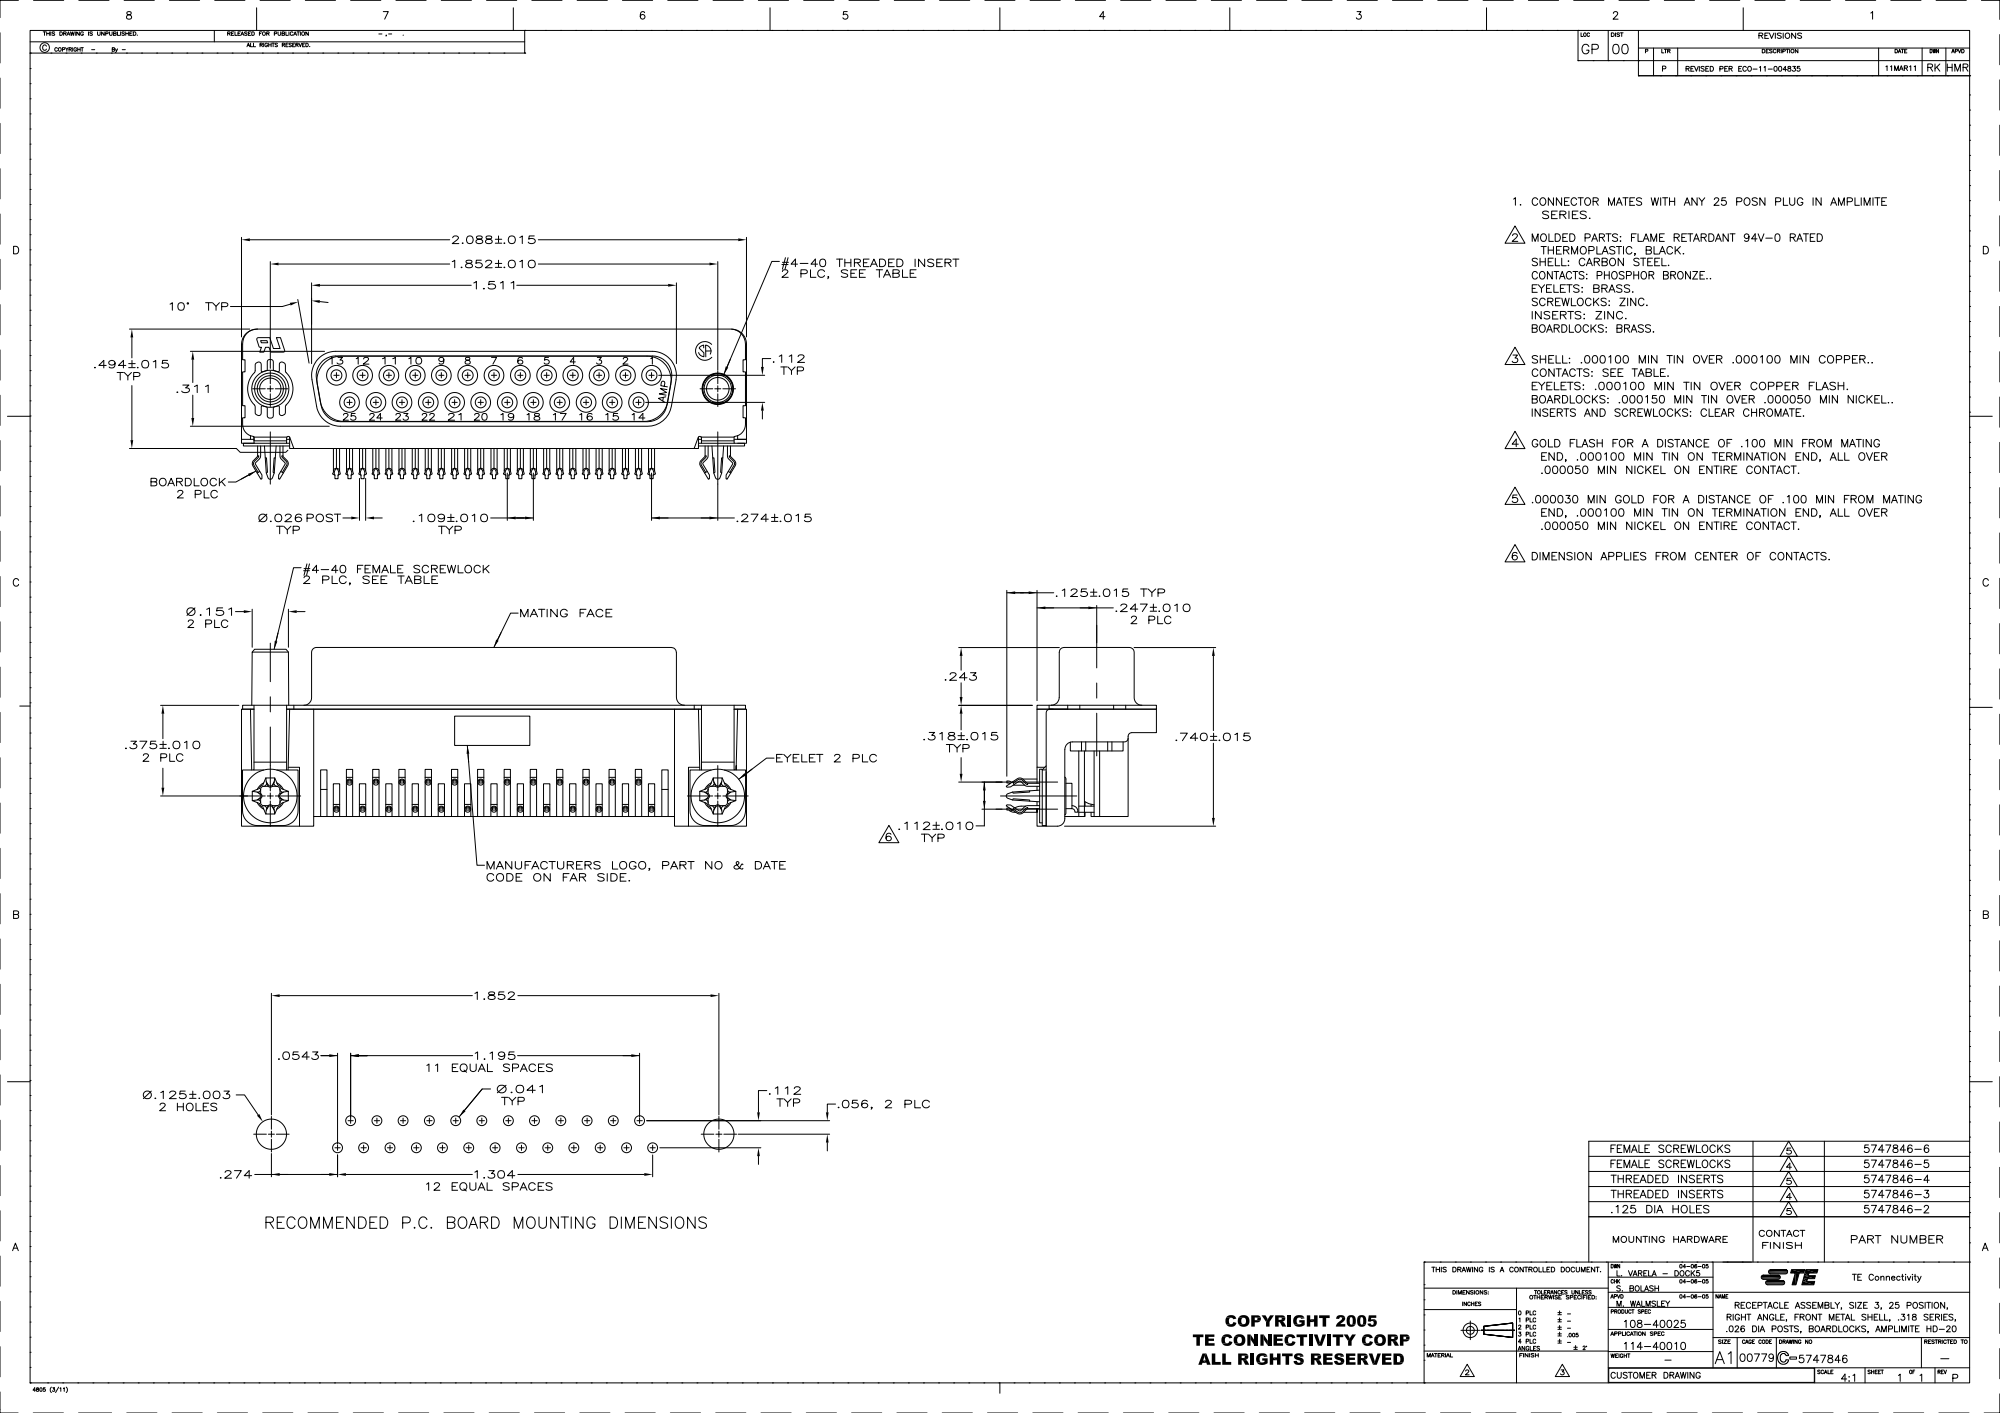
[picture p120: page 1]
