PubInv/Ox/mech/frontpanel/BottomPanelTechDrawVersion2.pdf

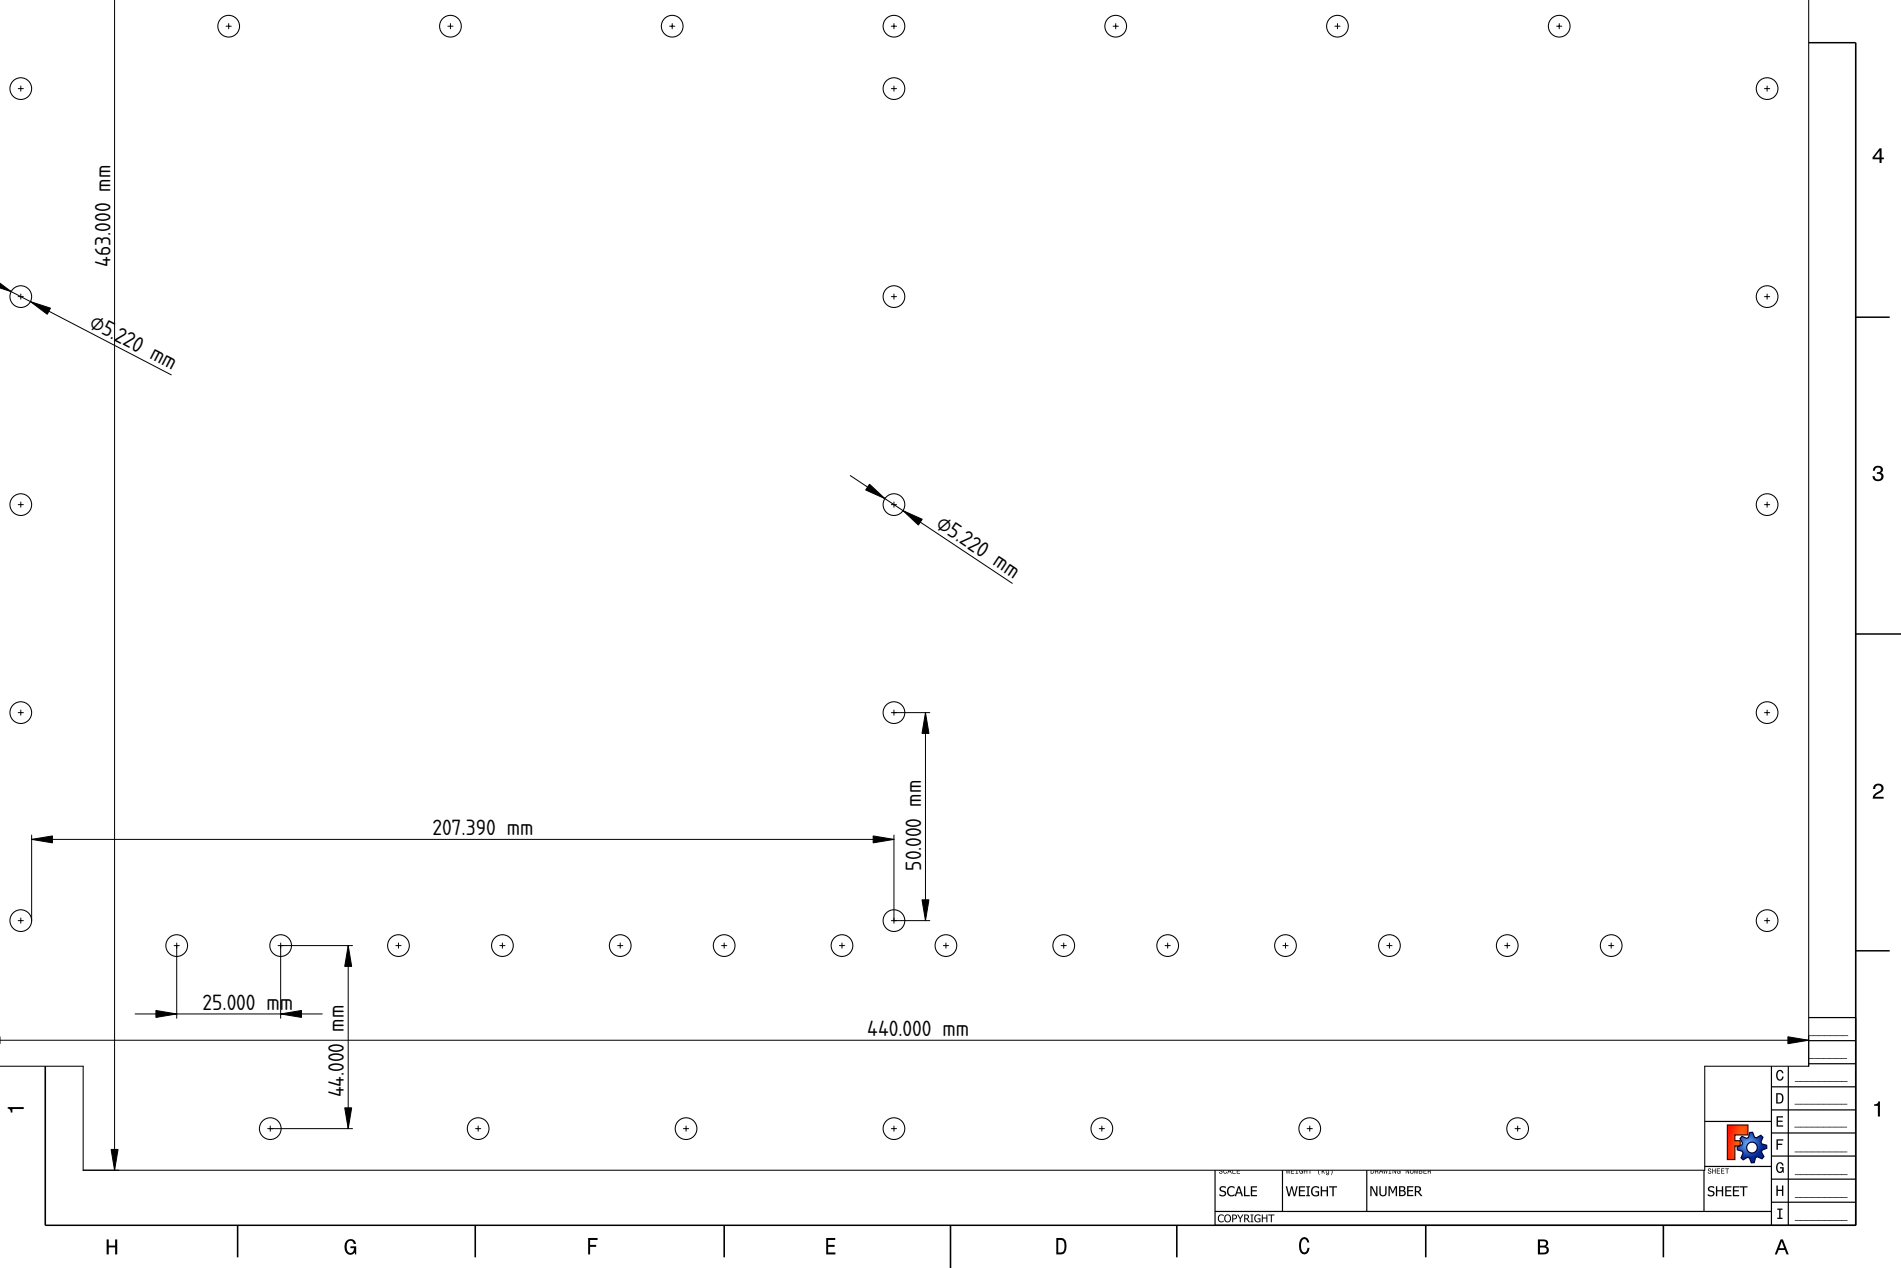
[picture p121: page 1]
