PubInv/Ox/mech/frontpanel/DIN_Rail_350mmx2.pdf

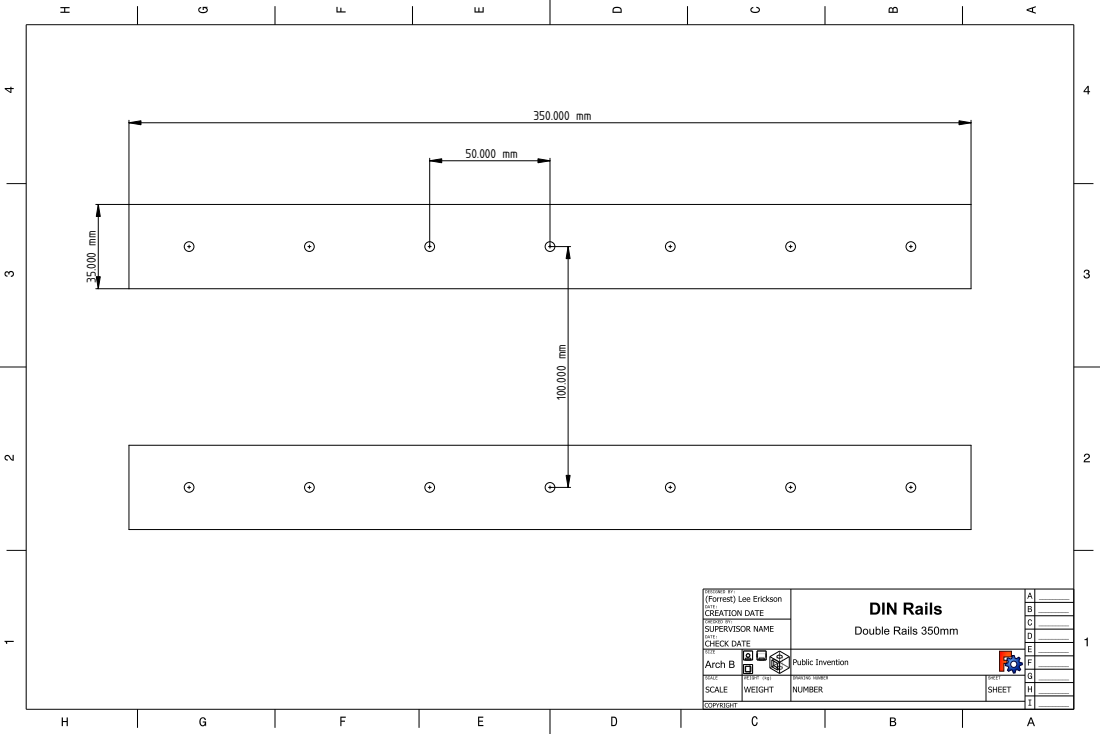
[picture p122: page 1]
