PubInv/Ox/mech/frontpanel/FrontPanelTechDrawVersion120230324_1124.pdf

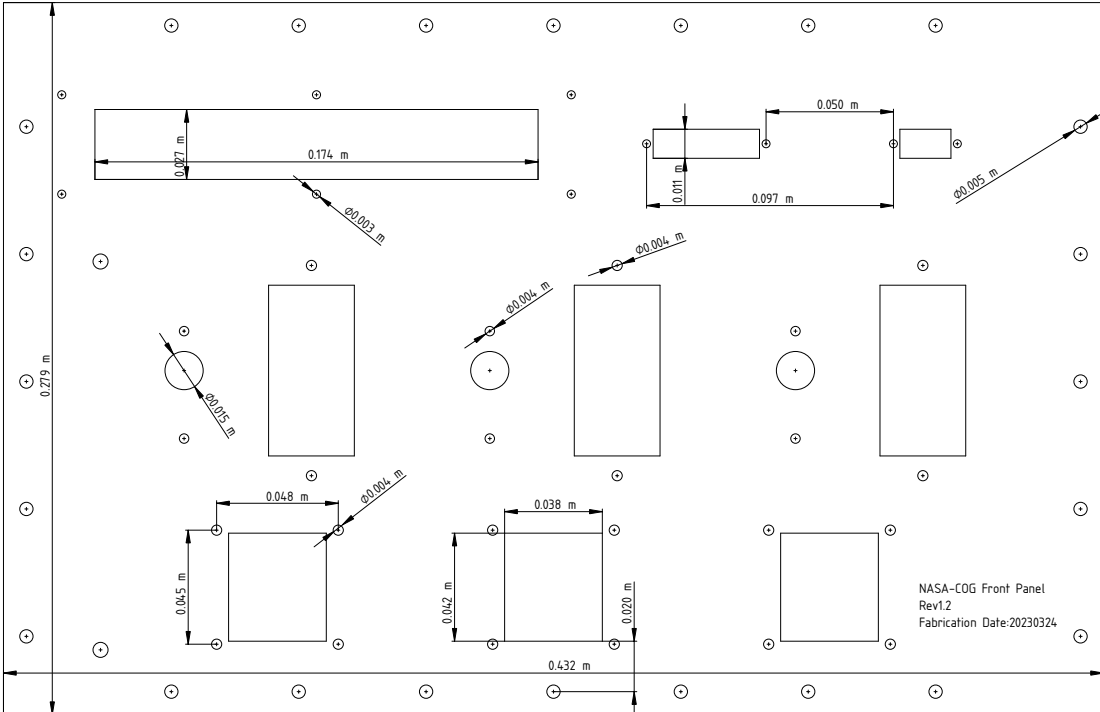
[picture p123: page 1]
Fro; el Rev1.2 Fabrication Date:202303
