PubInv/Ox/mech/frontpanel/FrontPanelTechDrawVersion120230405_1358.pdf

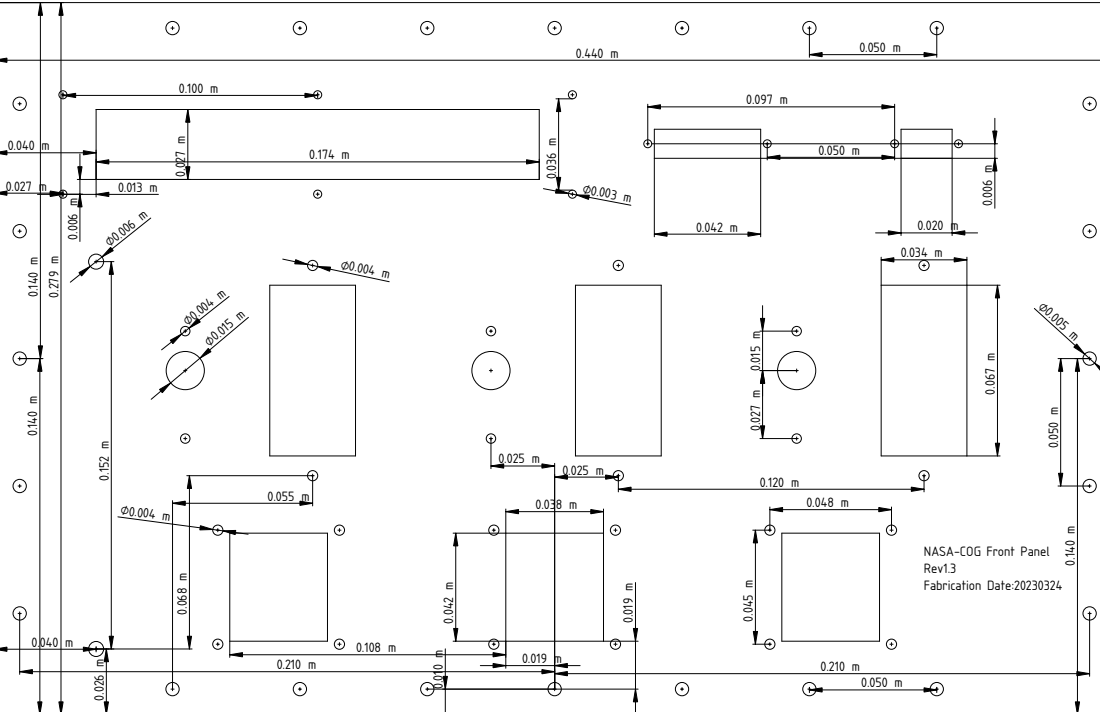
[picture p124: page 1]
Fro; el Rev1.3 Fabrication Date:202303
