PubInv/Ox/mech/frontpanel/FrontPanelTechDrawVersion2.0_20230731_0802.pdf

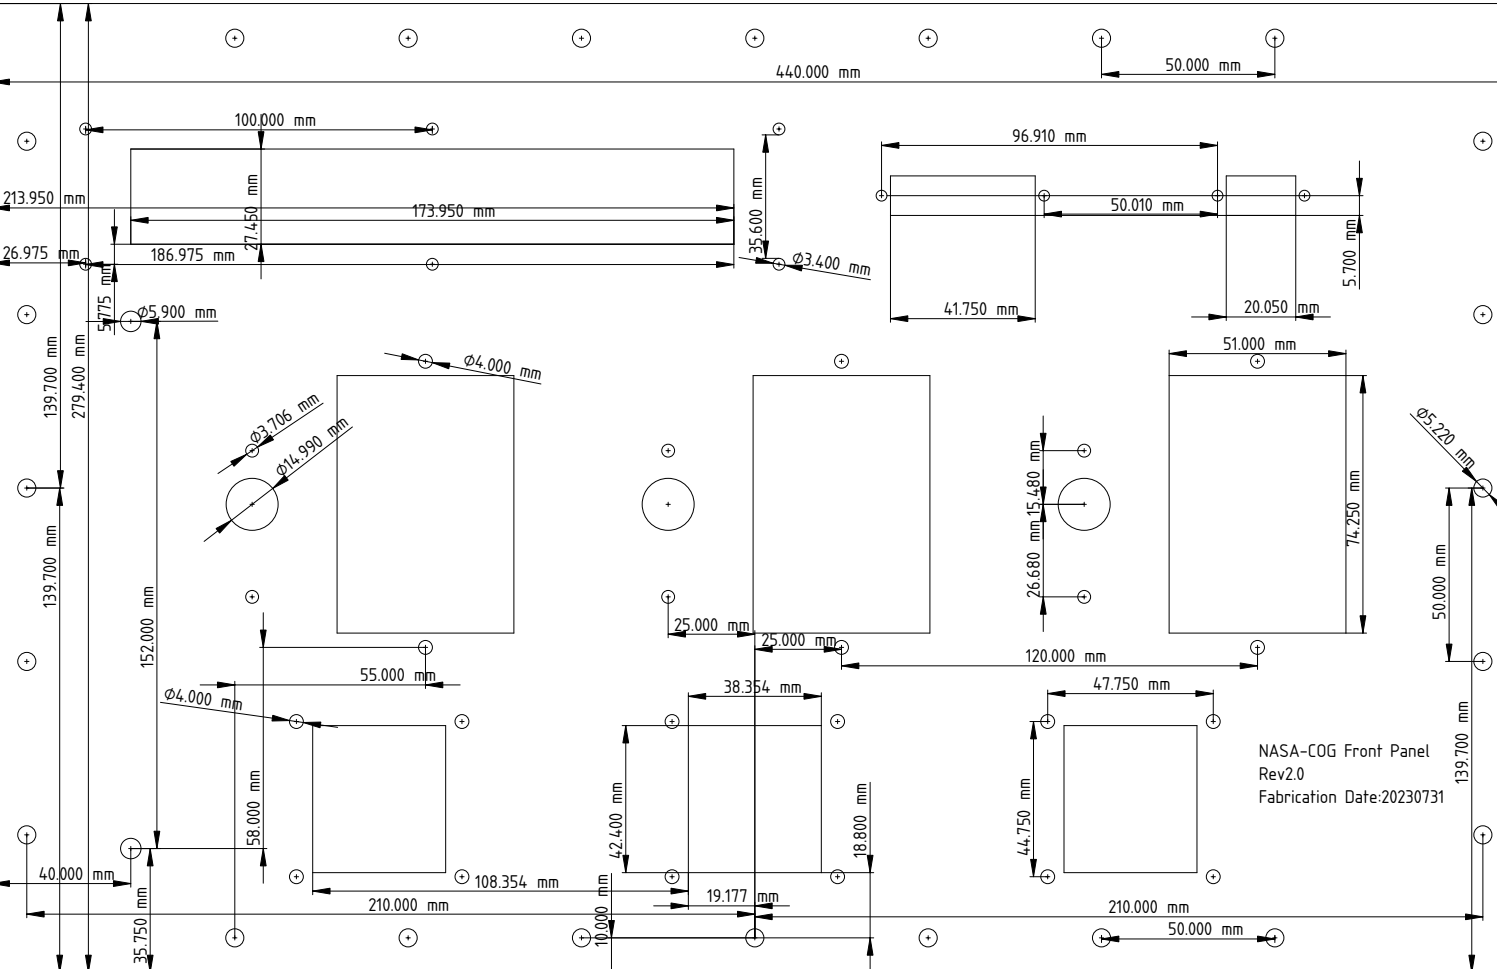
[picture p125: page 1]

NASA-COG Front Panel
Rev2.0 Fabrication Date:20230731
