PubInv/Ox/mech/frontpanel/PlantPanelFrontLeft.pdf

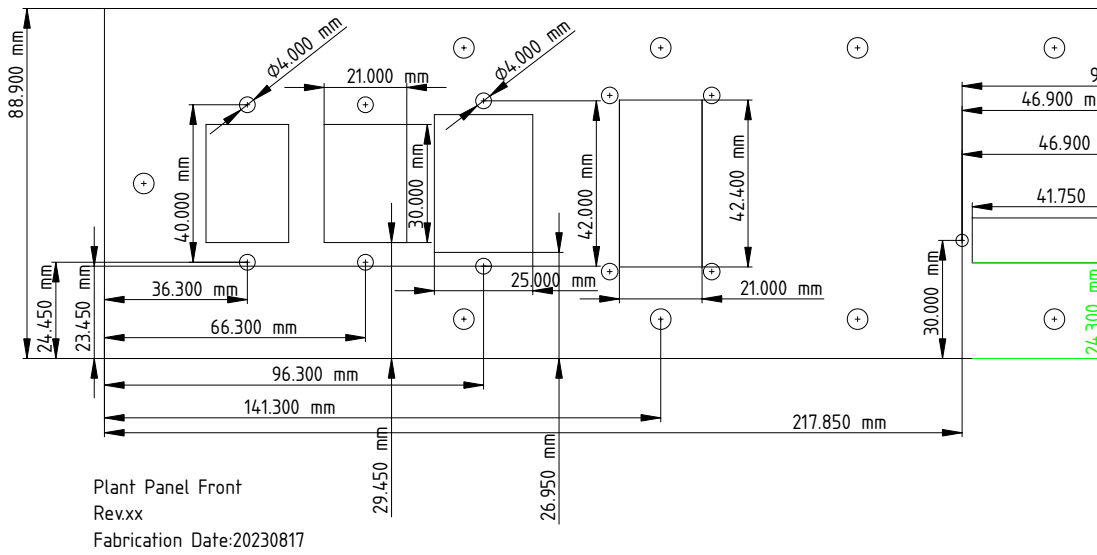
[picture p126: page 1]
Pla; el Fro

nt Rev.xx Fabrication Date:2
