PubInv/Ox/mech/frontpanel/PlantPanelFrontRight.pdf

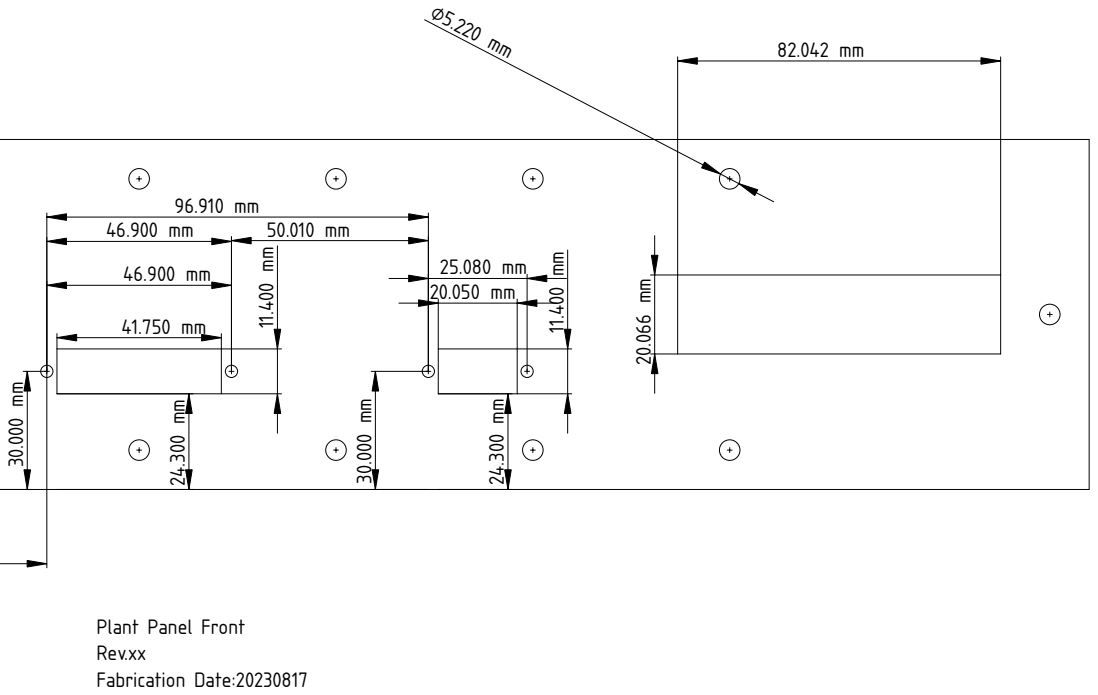
[picture p127: page 1]

Plant Panel Front
Rev.xx
Fabrication Date:20230817
