PubInv/Ox/elec/Control Board/Control v1/ControlV1_PCB_Color.pdf

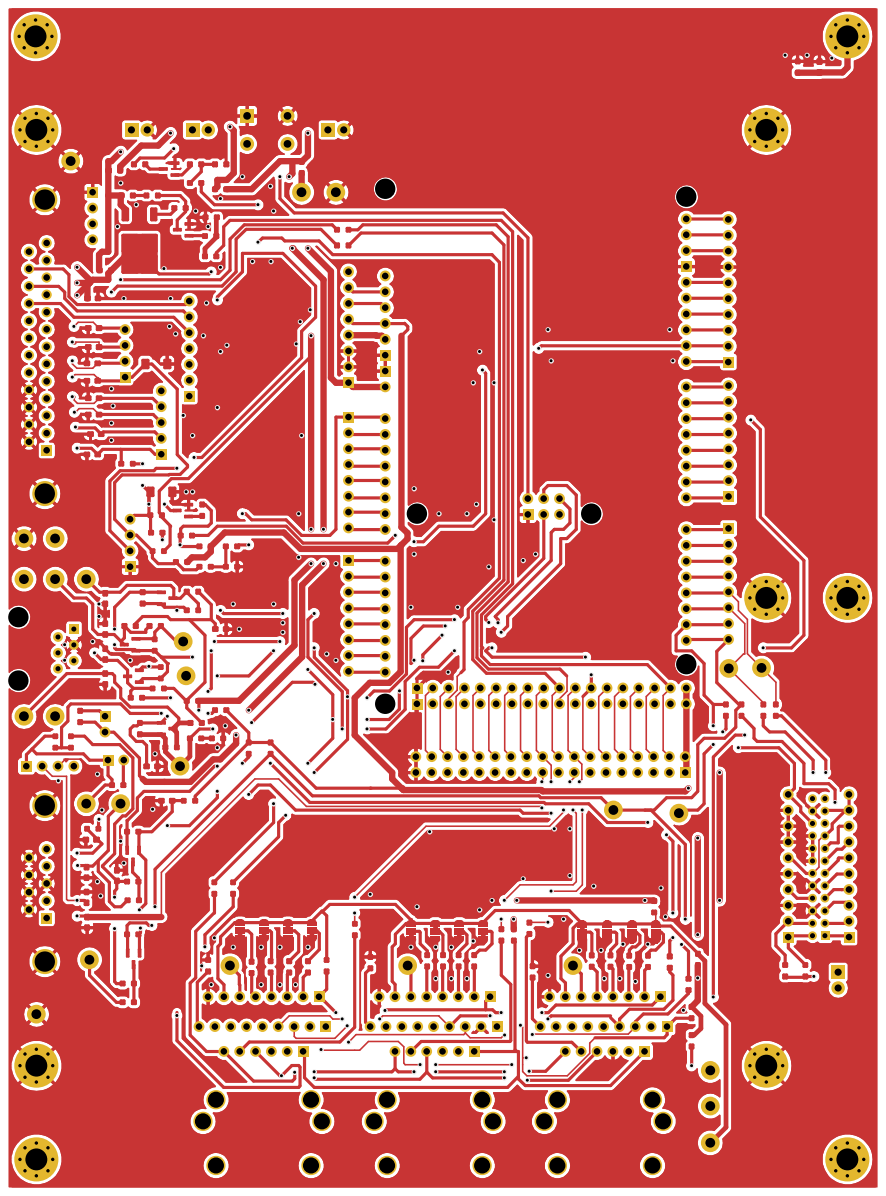
[picture p128: page 1]

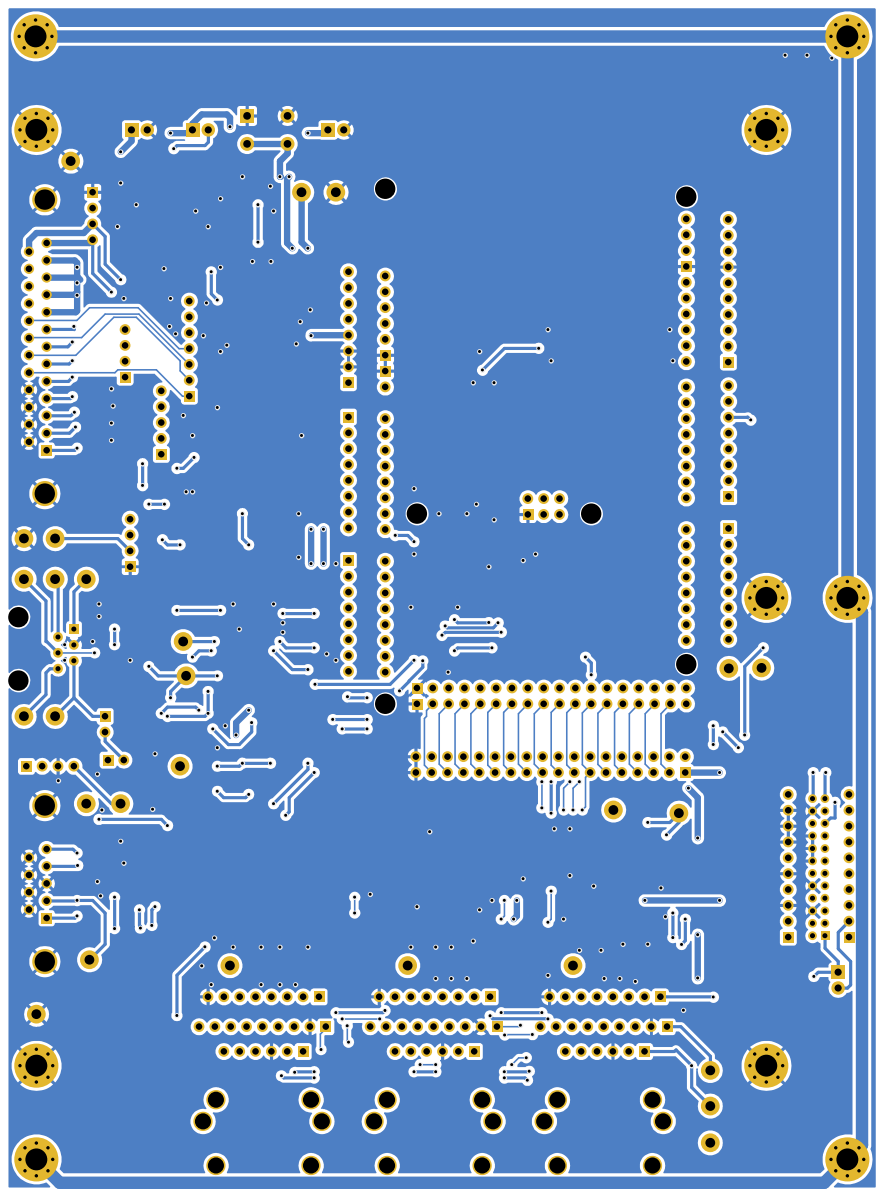
[picture p129: page 2]

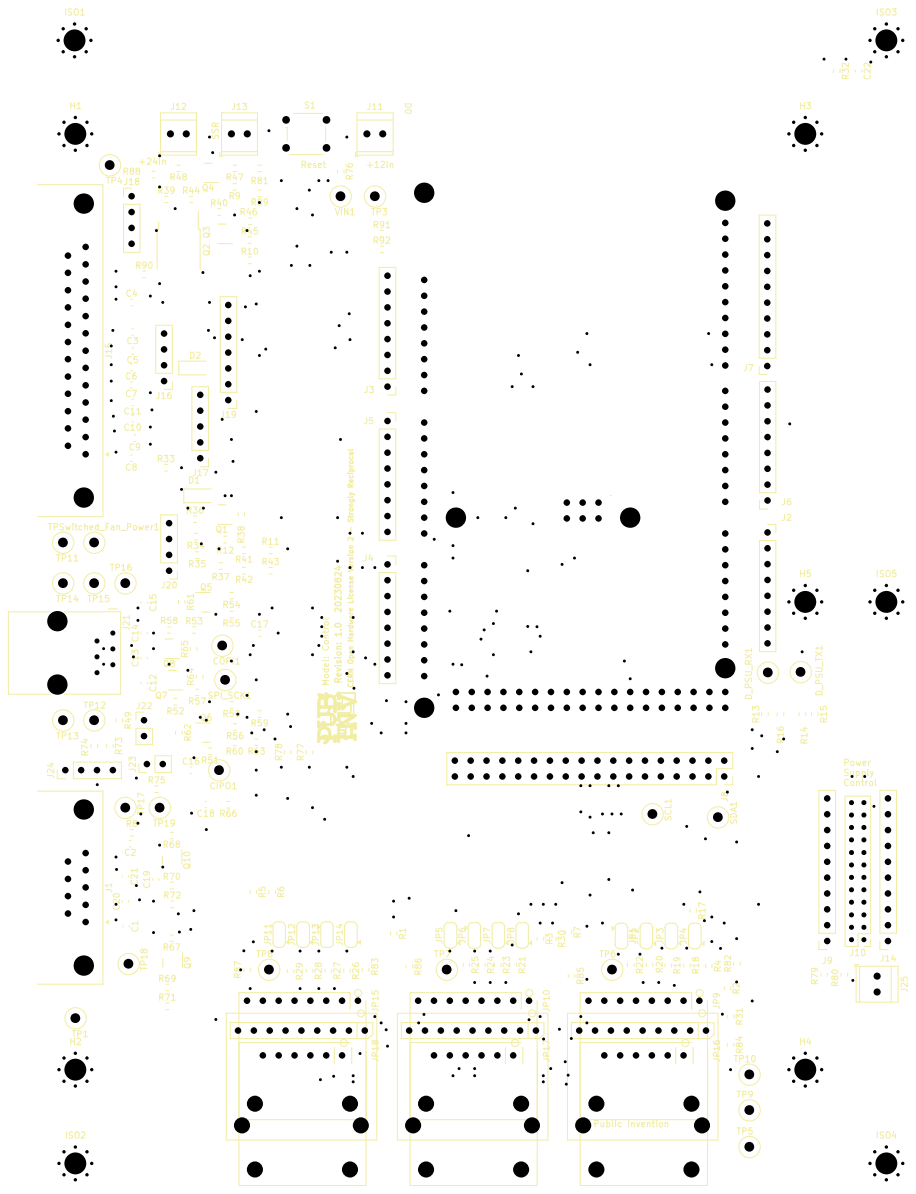
[picture p130: page 3]

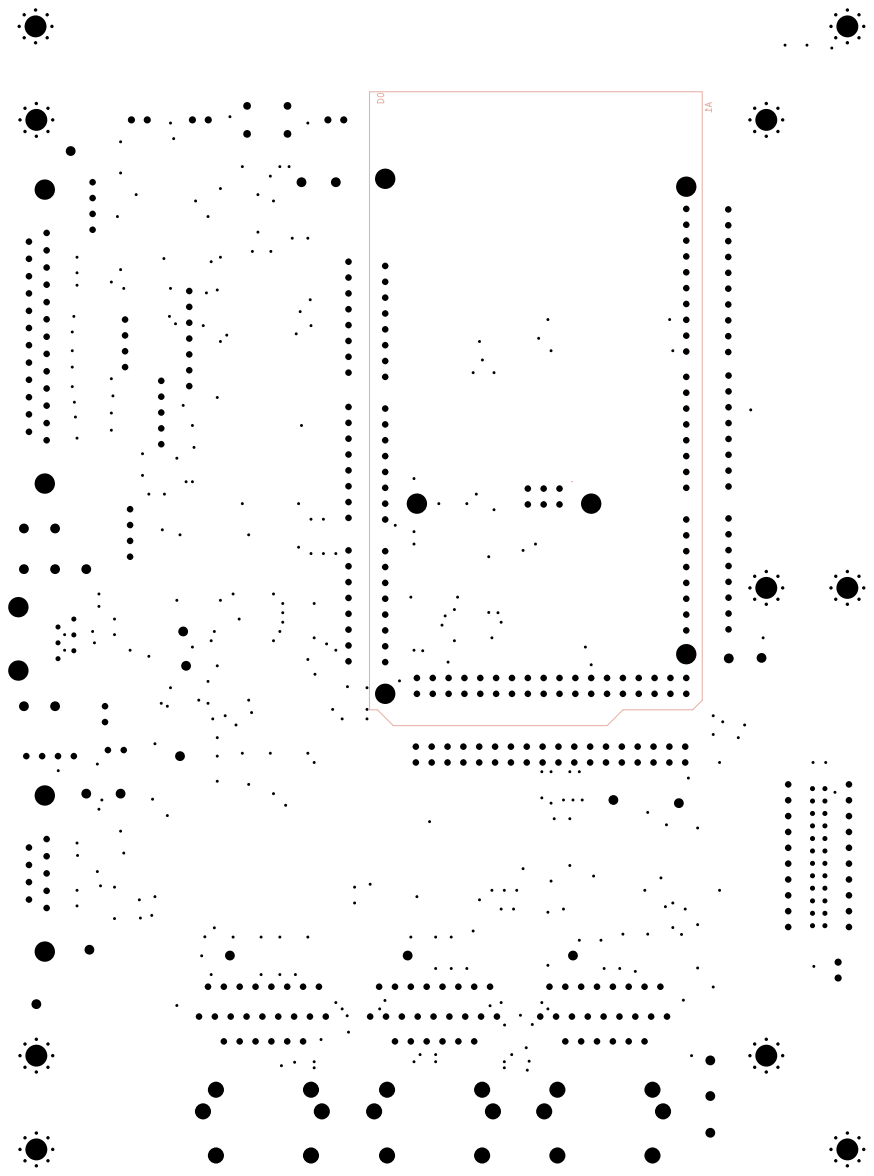
[picture p131: page 4]

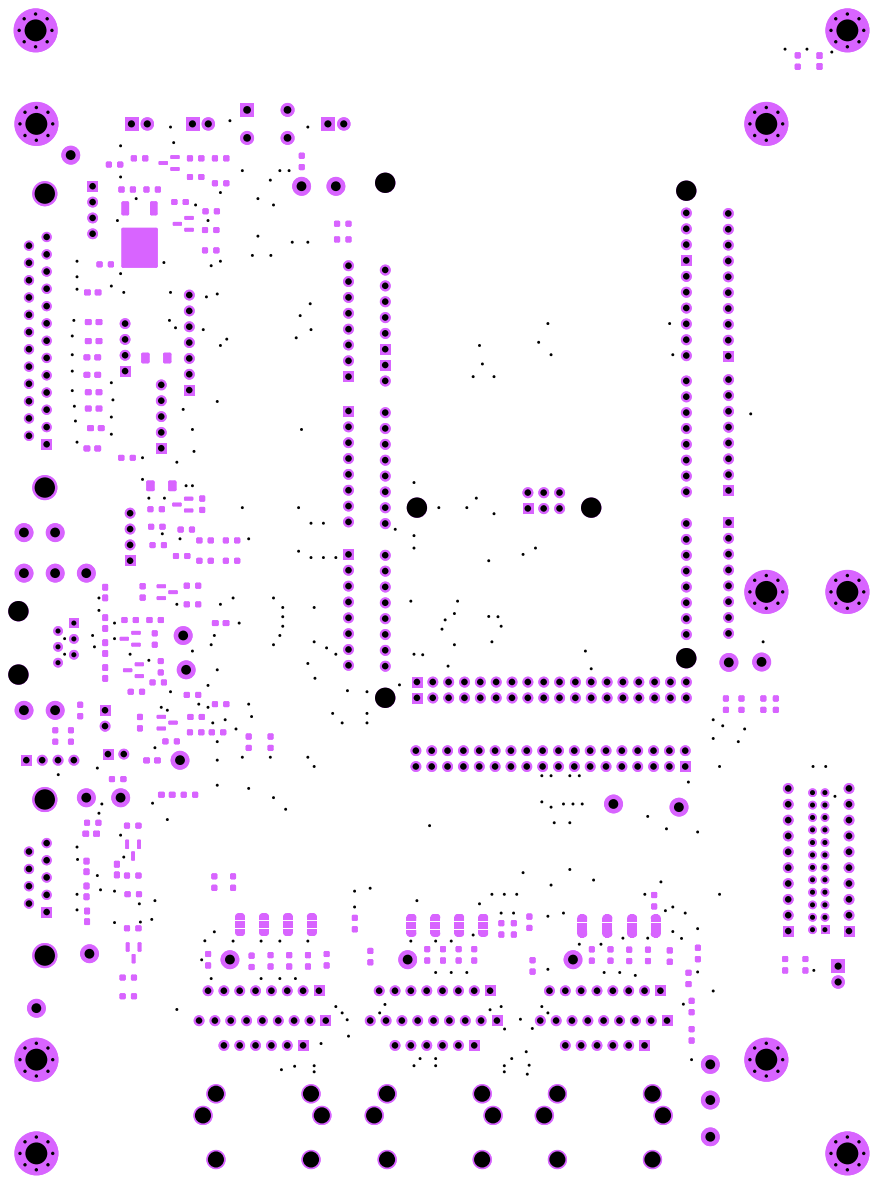
[picture p132: page 5]

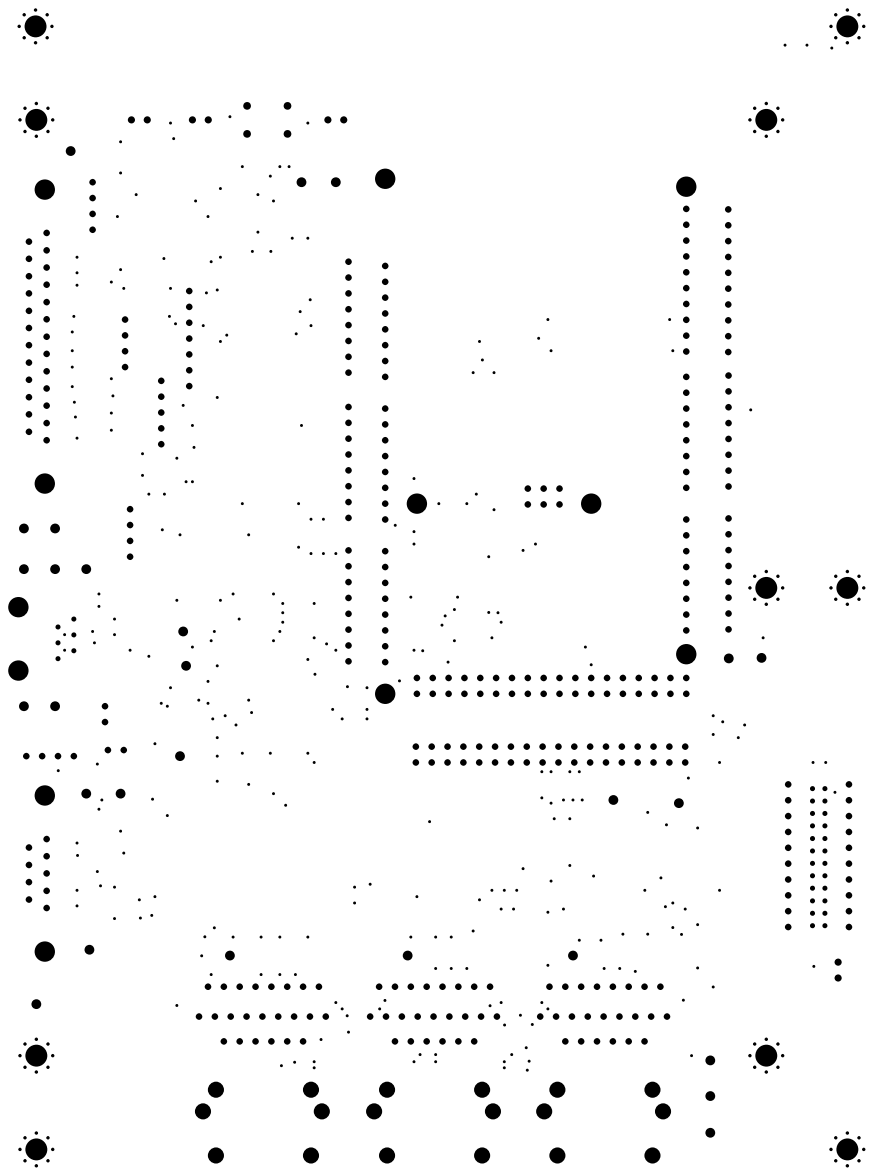
[picture p133: page 6]

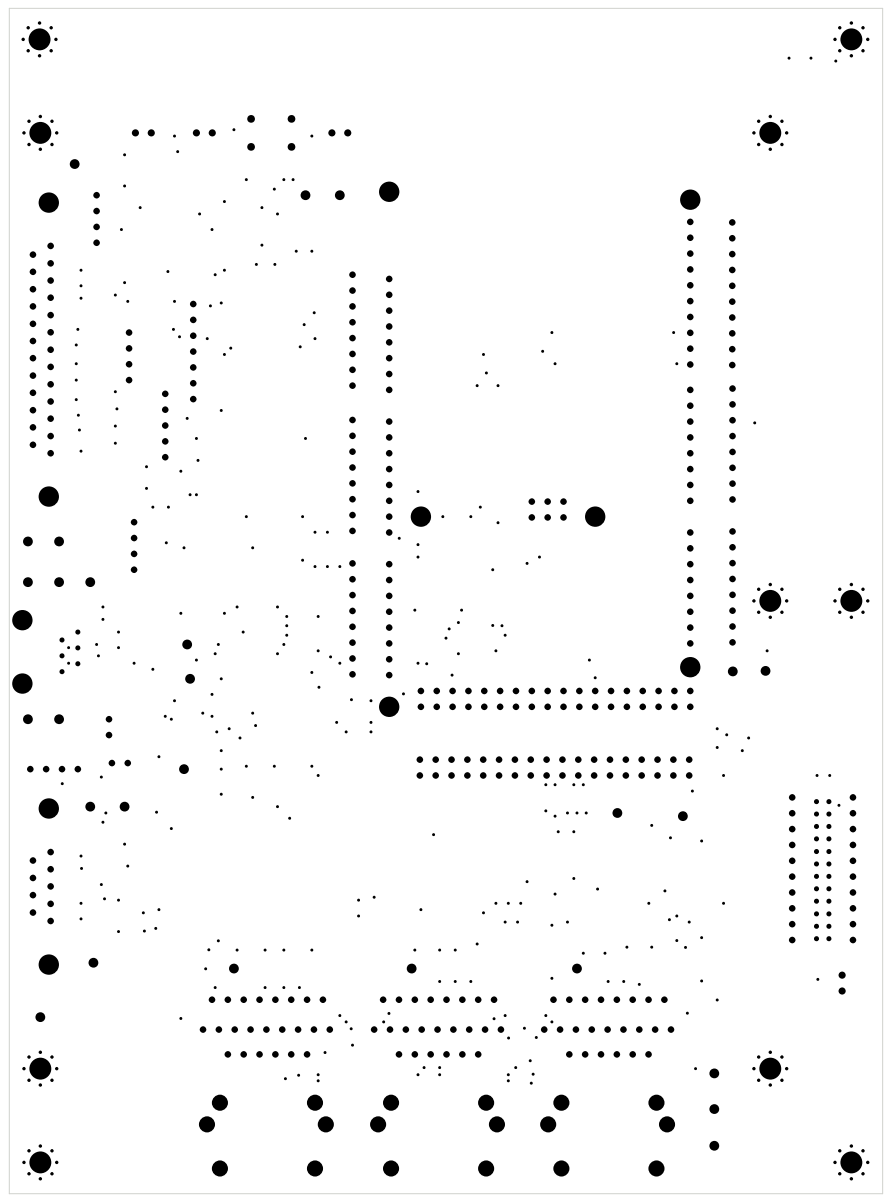
[picture p134: page 7]

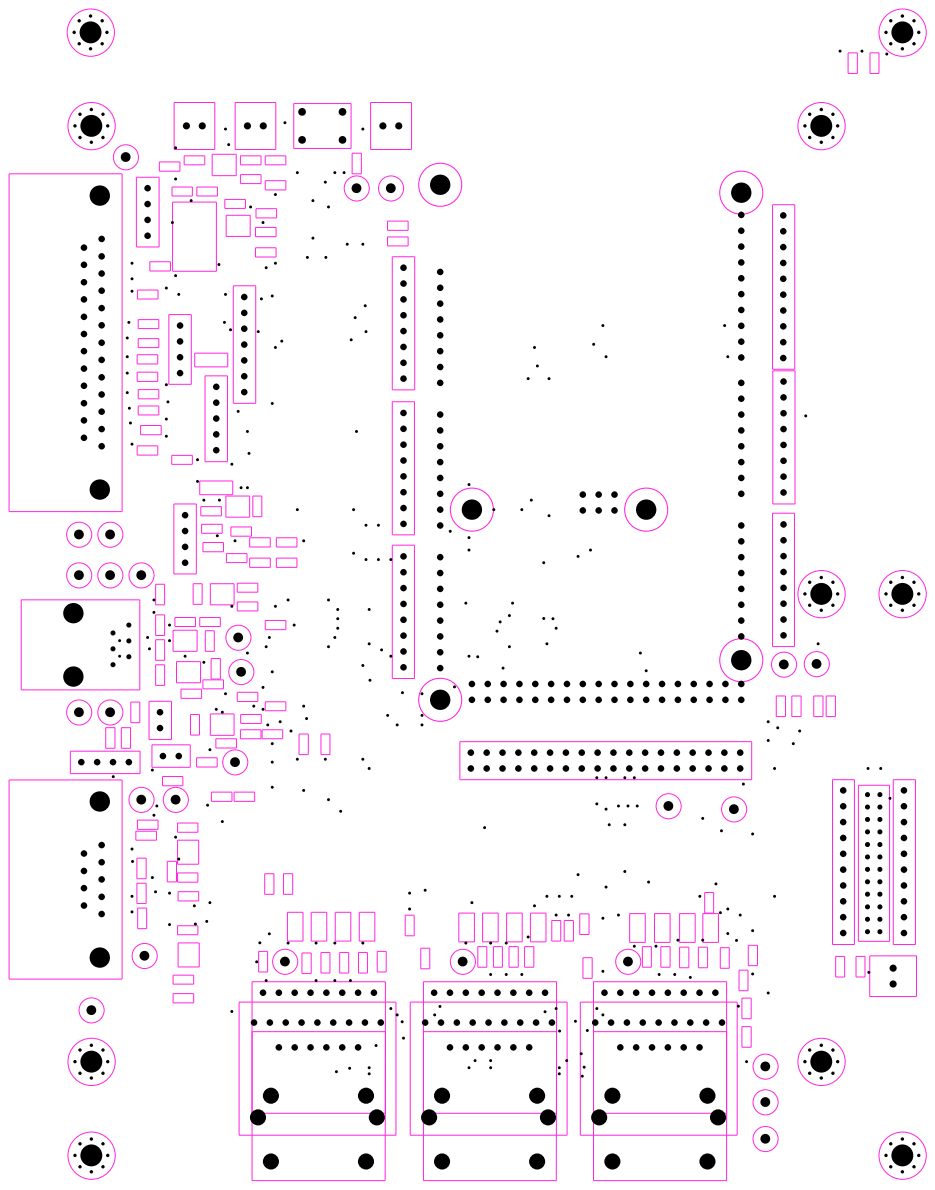
[picture p135: page 8]

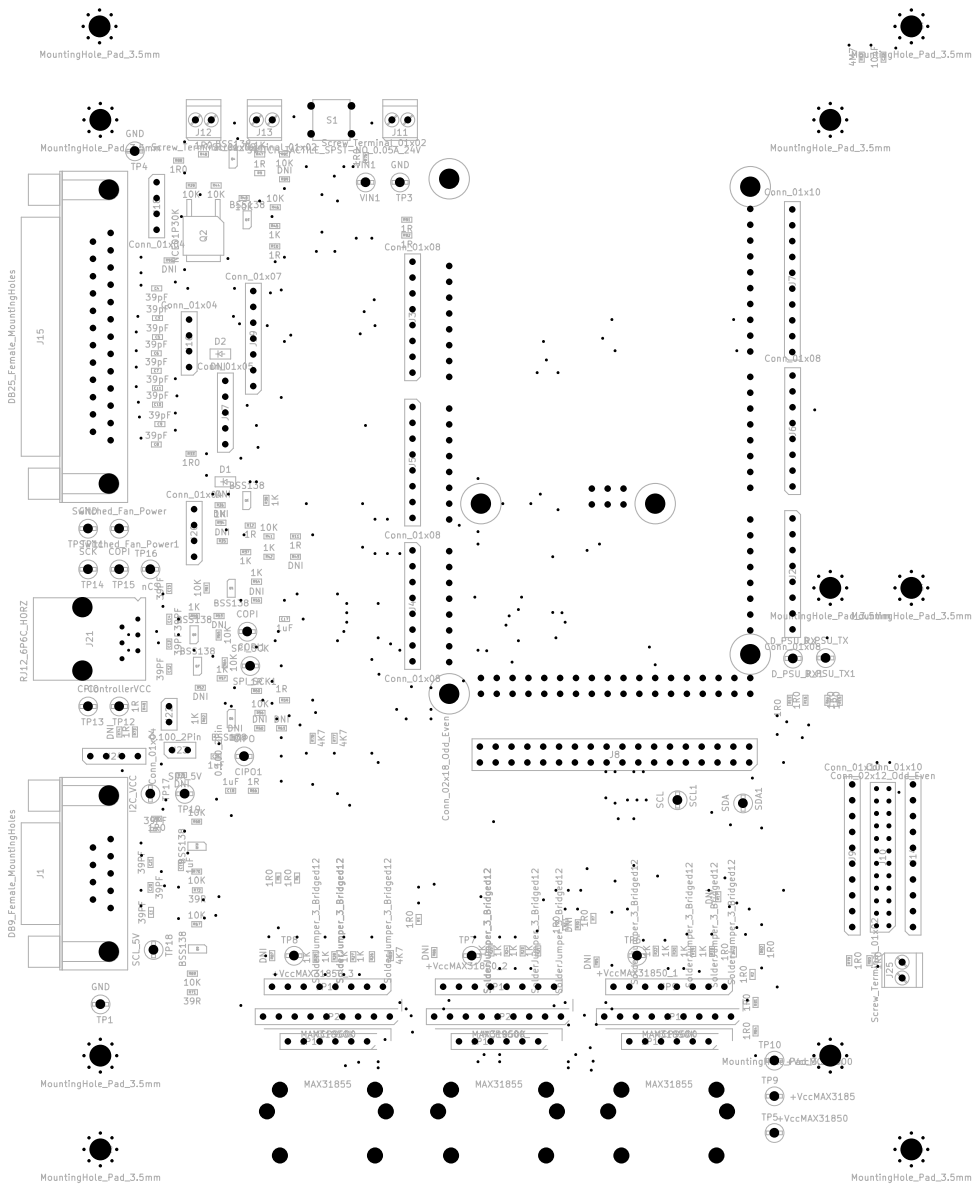
[picture p136: page 9]
