PubInv/Ox/elec/Control Board/Control v1/resources/DB25/C190083_D-DMR025PF-D002.pdf

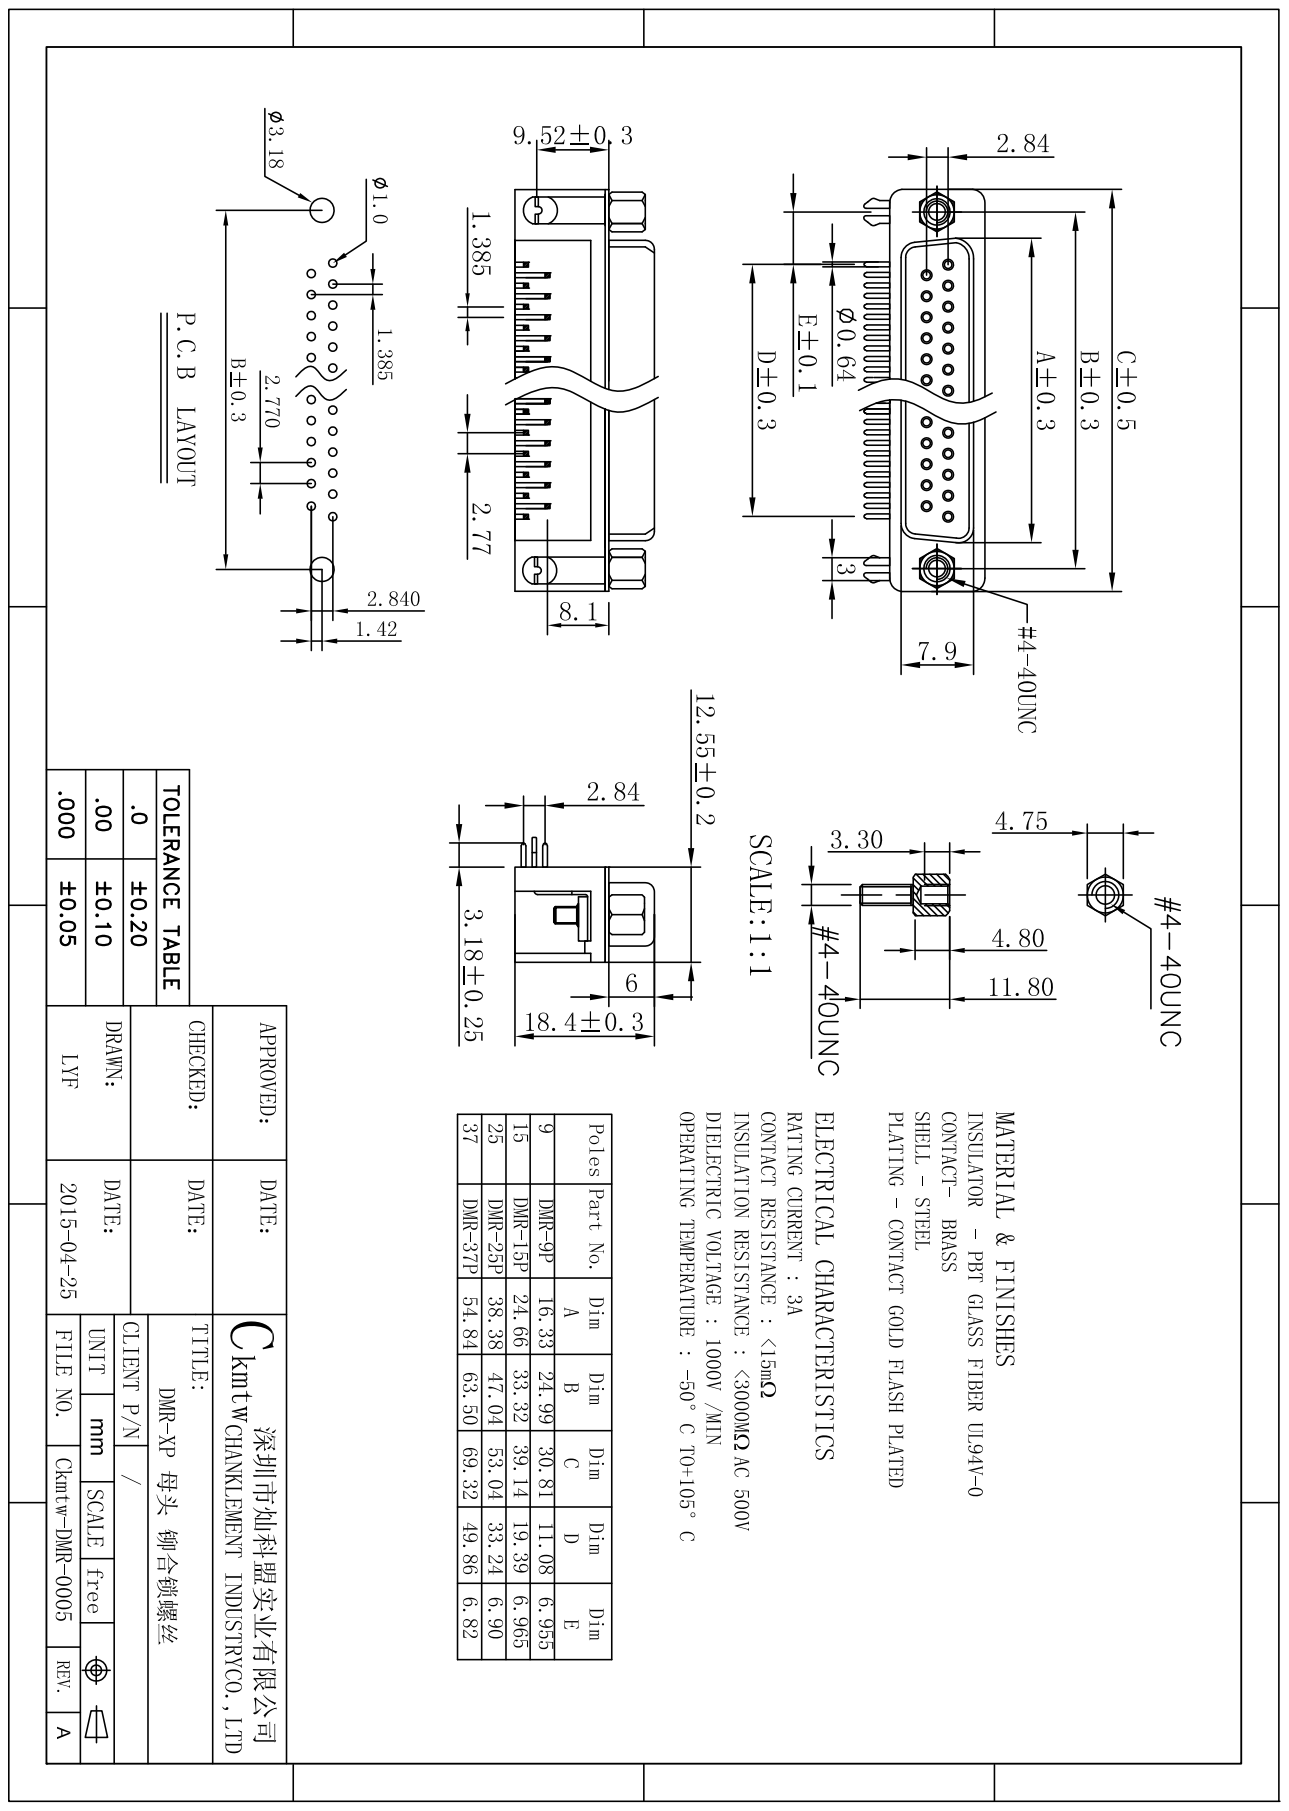
[picture p137: page 1]
