PubInv/Ox/elec/Control Board/Control v1/resources/DB25/C77838_DS1037-25FNAKT74-0CC.pdf

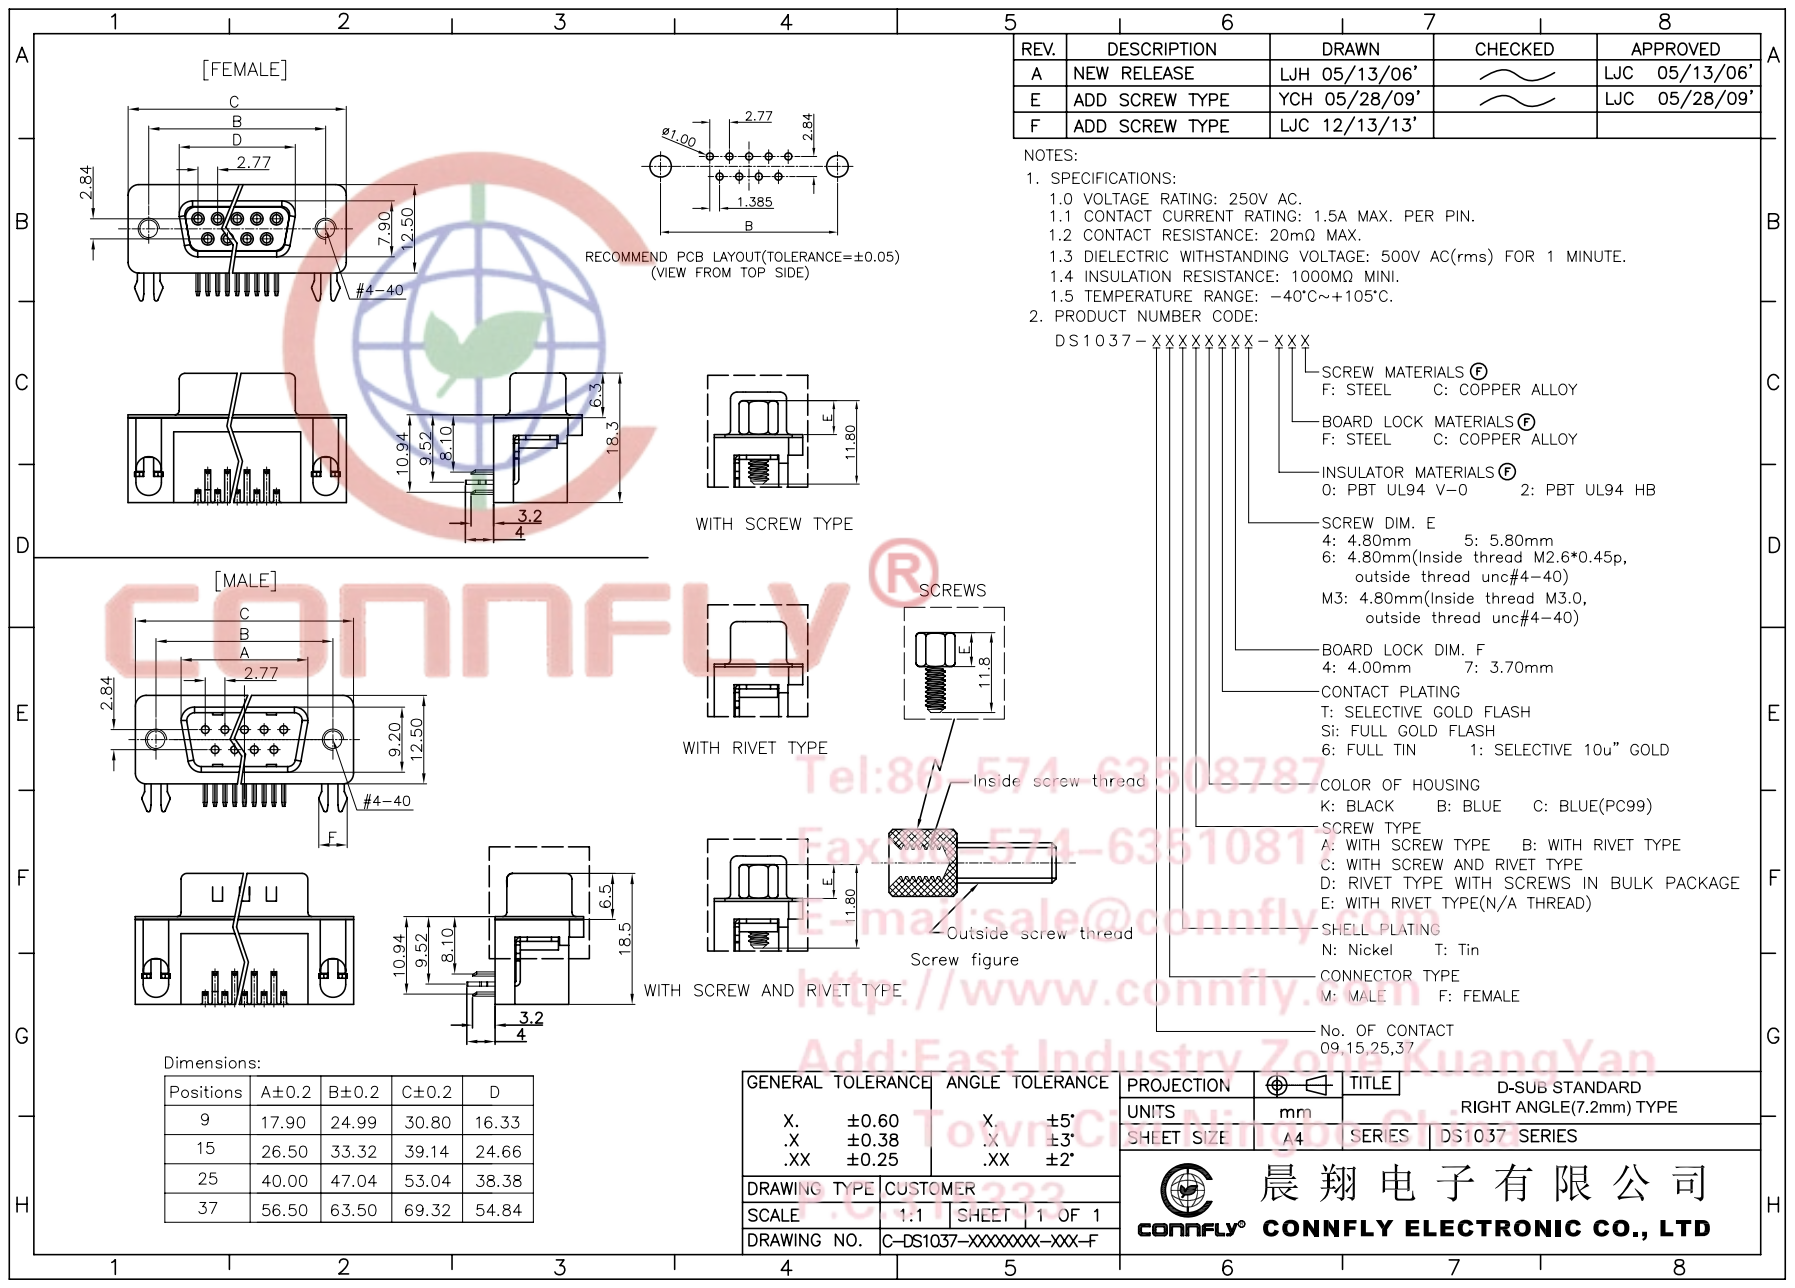
[picture p138: page 1]
