PubInv/Ox/elec/Control Board/Control v1/resources/FemaleHeader_2x18/C132131_DS1023-2_18SF11.pdf

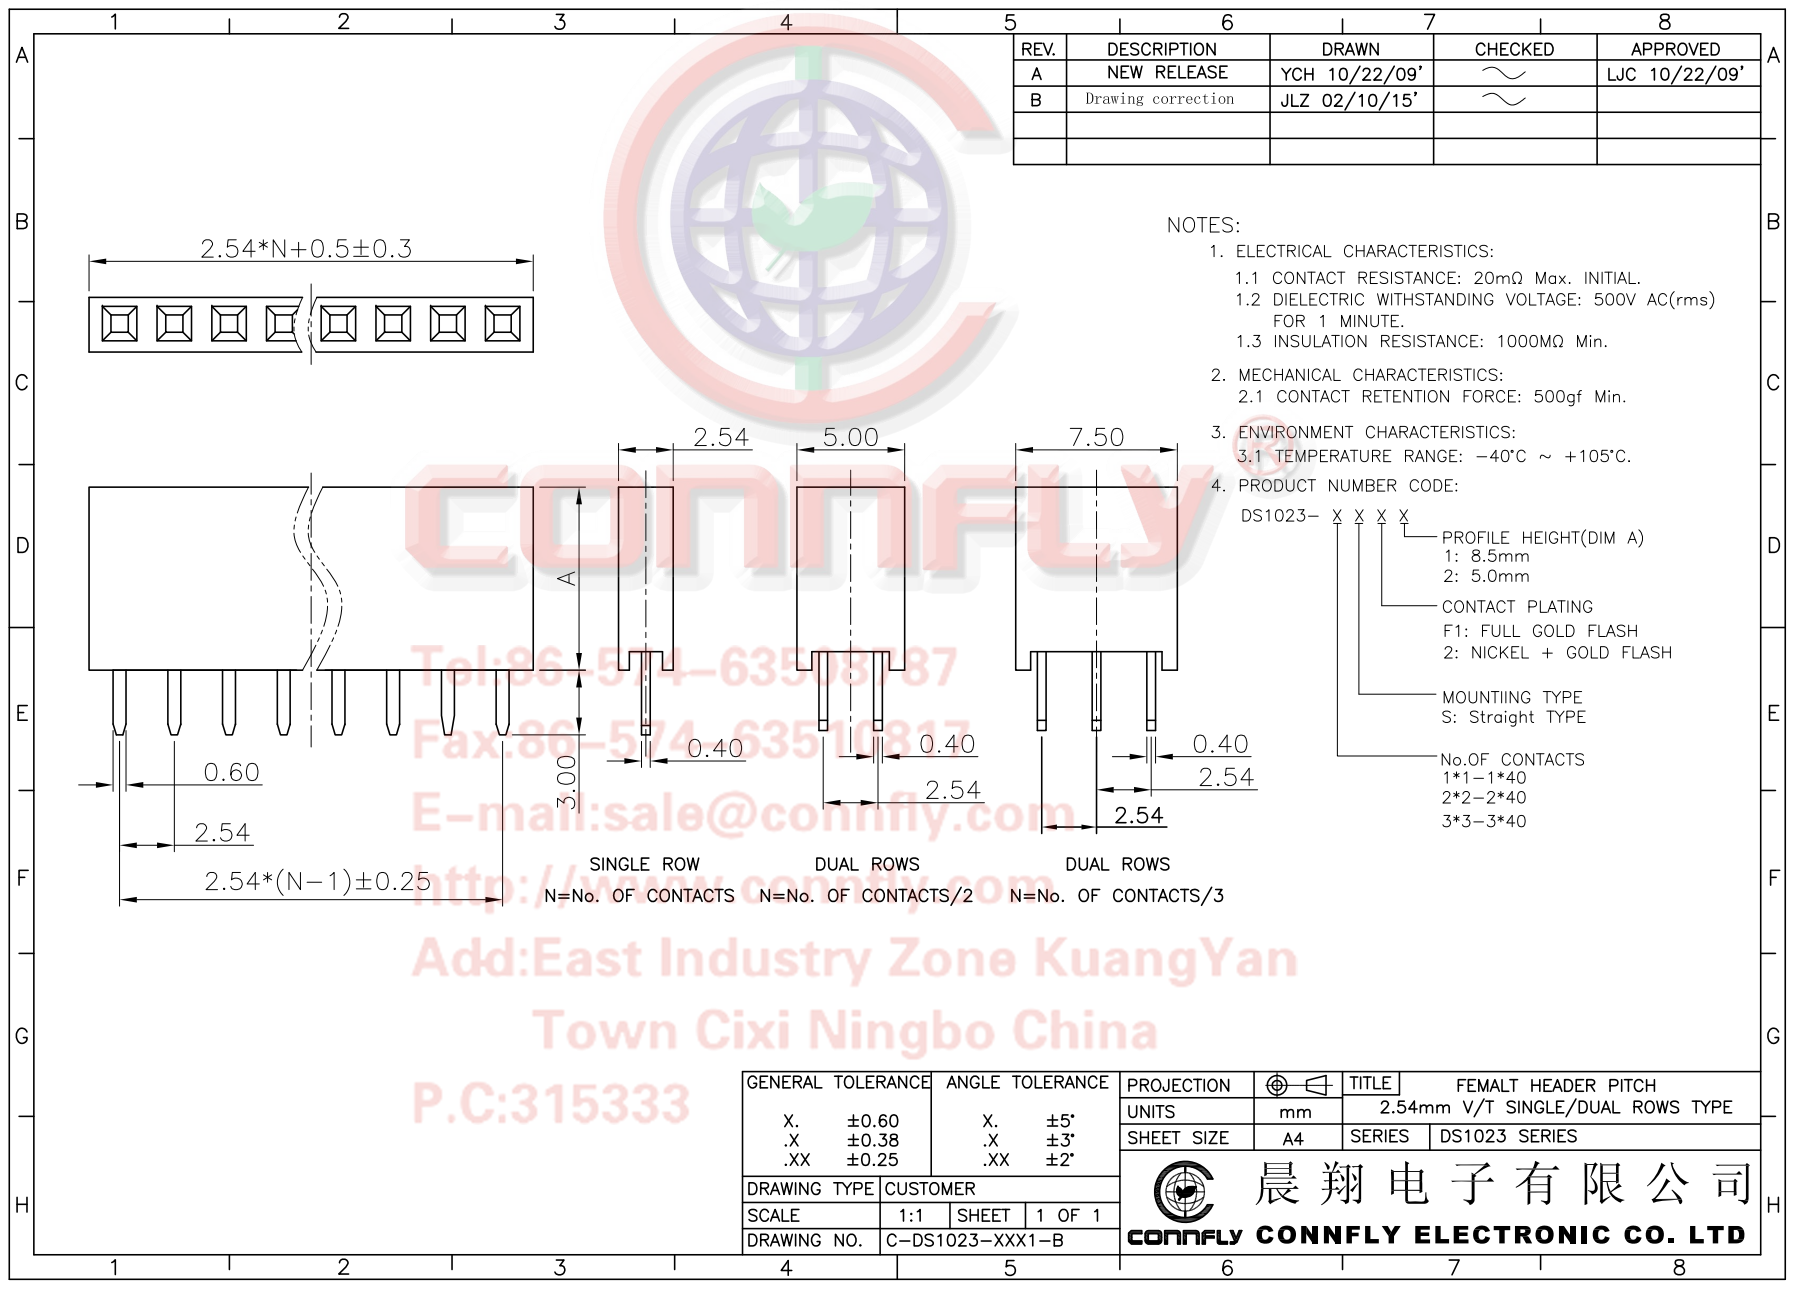
[picture p139: page 1]
