PubInv/Ox/docs/OEDCS_June_2023_Version_0.1/Photos/FanControllerPCB(unpopulated).JPG

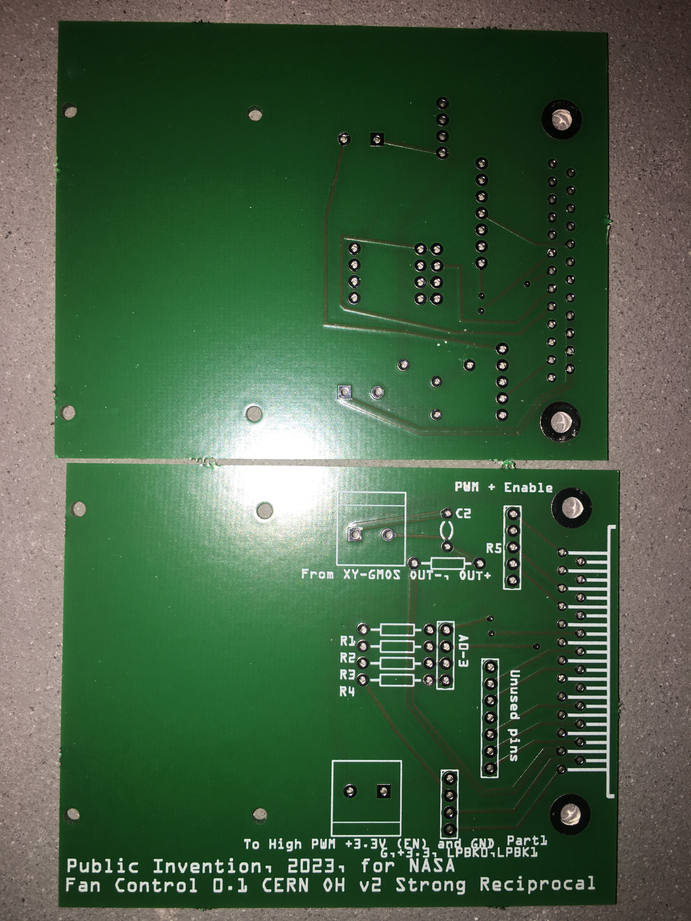
docs/OEDCS_June_2023_Version_0.1/Photos/FanControllerPCB(unpopulated).JPG
